ecilasun/tinysys/software/emulator/sdcard/jpeg/flowers.jpg

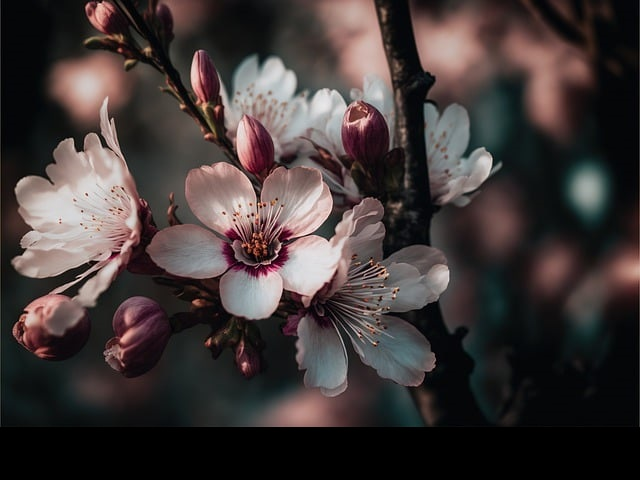
software/emulator/sdcard/jpeg/flowers.jpg
