ecilasun/tinysys/mechanical/expansionboardA.SLDASM

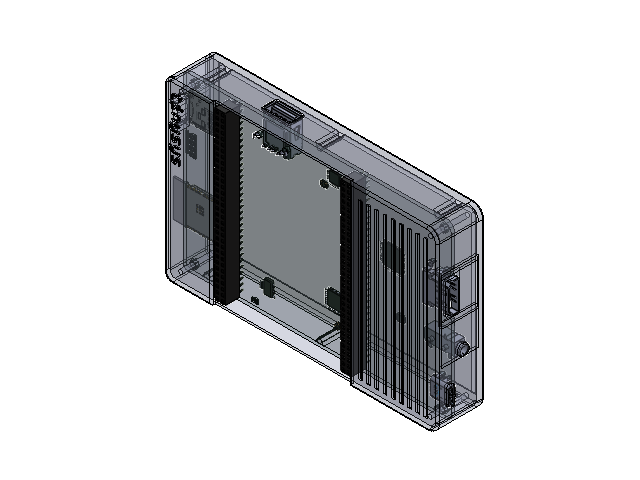
[picture p31: CAD file, 2024-03-18]
mechanical/expansionboardA.SLDASM
CUI_DEVICES_HD02-19-M-MSMT-TR-0
USB4085-GF-A
SJ-3523-SMT-TR-3
LM1117-3
TQFP_64_10x10mm_P05mm
PinSocket_2x32_P254mm_Vertical x 2
LED_1206_3216Metric-5 x 5
DM3AT-SF-PEJM5-6
403WF32015HKR x 2
C32+1
ESP32-C6-WROOM-1_V1
expansionboardA_PCB
Part21^expansionboardA
Part22^expansionboardA
case
