ecilasun/tinysys/software/emulator/sdcard/jpeg/test.jpg

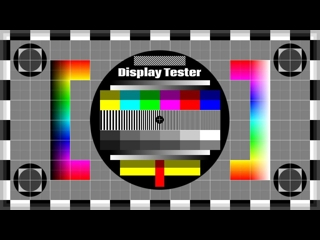
software/emulator/sdcard/jpeg/test.jpg
