ecilasun/tinysys/documents/XILINX-XC7A35T_100T_200T-CORE-BOARD-20220721-V01.pdf

## 5V ONLY

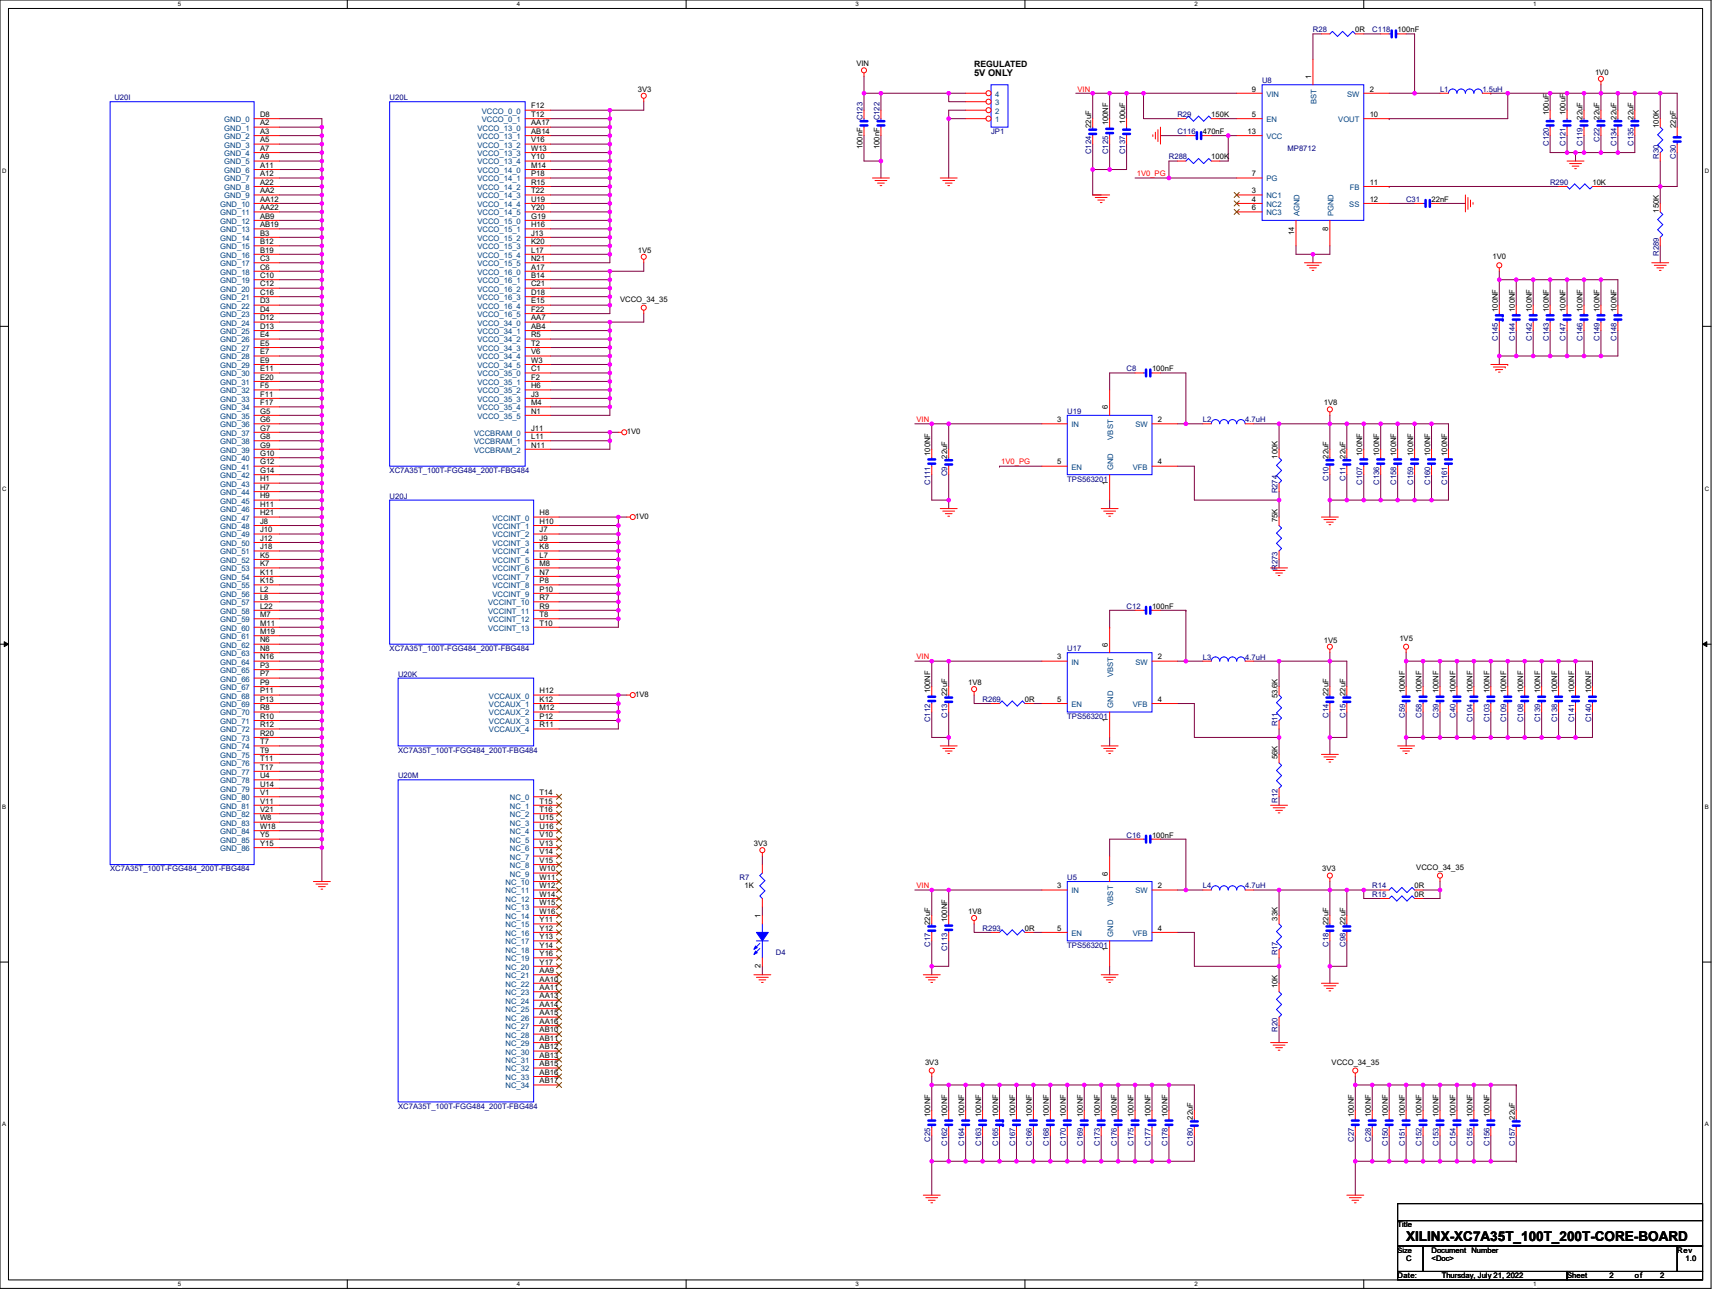
[picture p33: page 1]

Size C C C | Document Number <Doc> | Rev 1.0

Date: Thursday, July 21, 2022 | Sheet 2 of 2

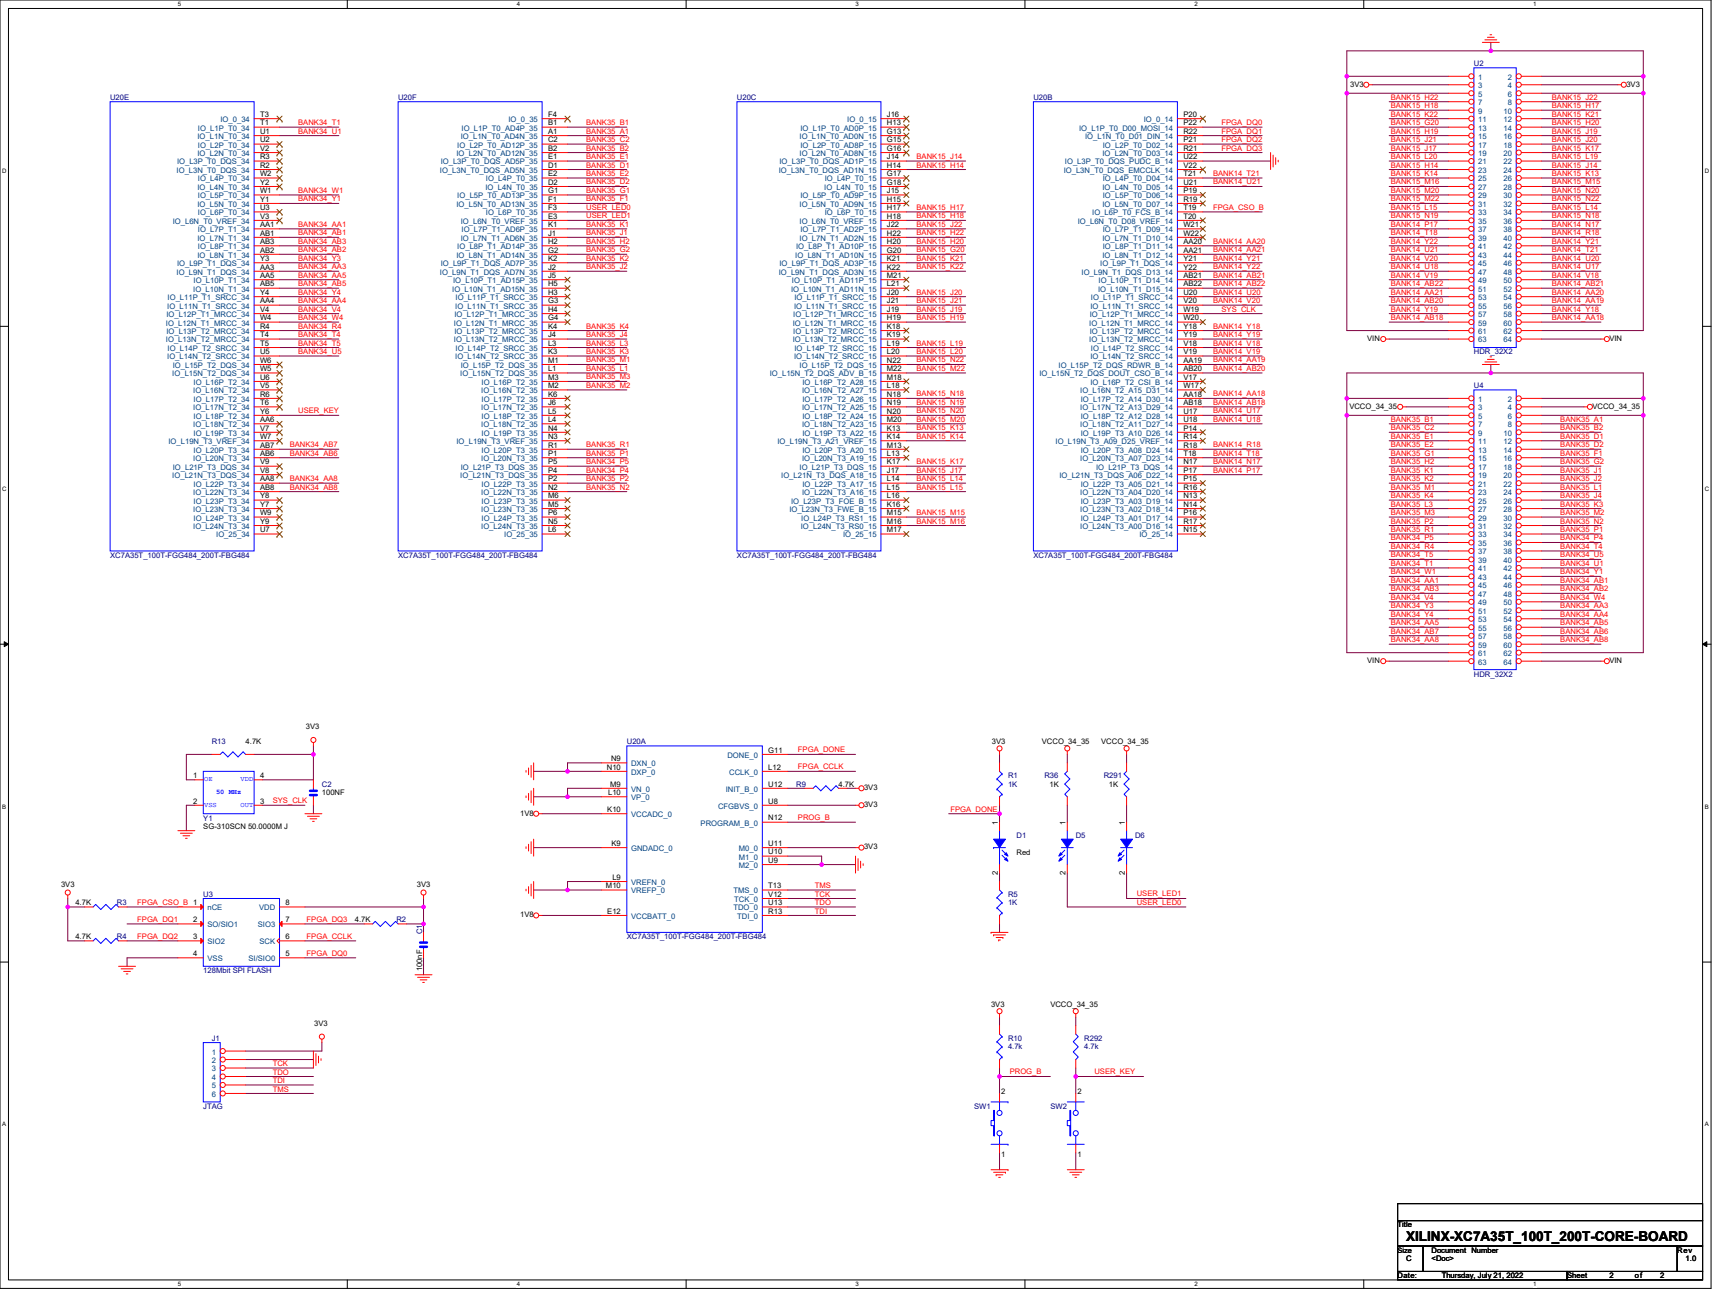
[picture p34: page 2]

D | D

# 100 ohms differential trace

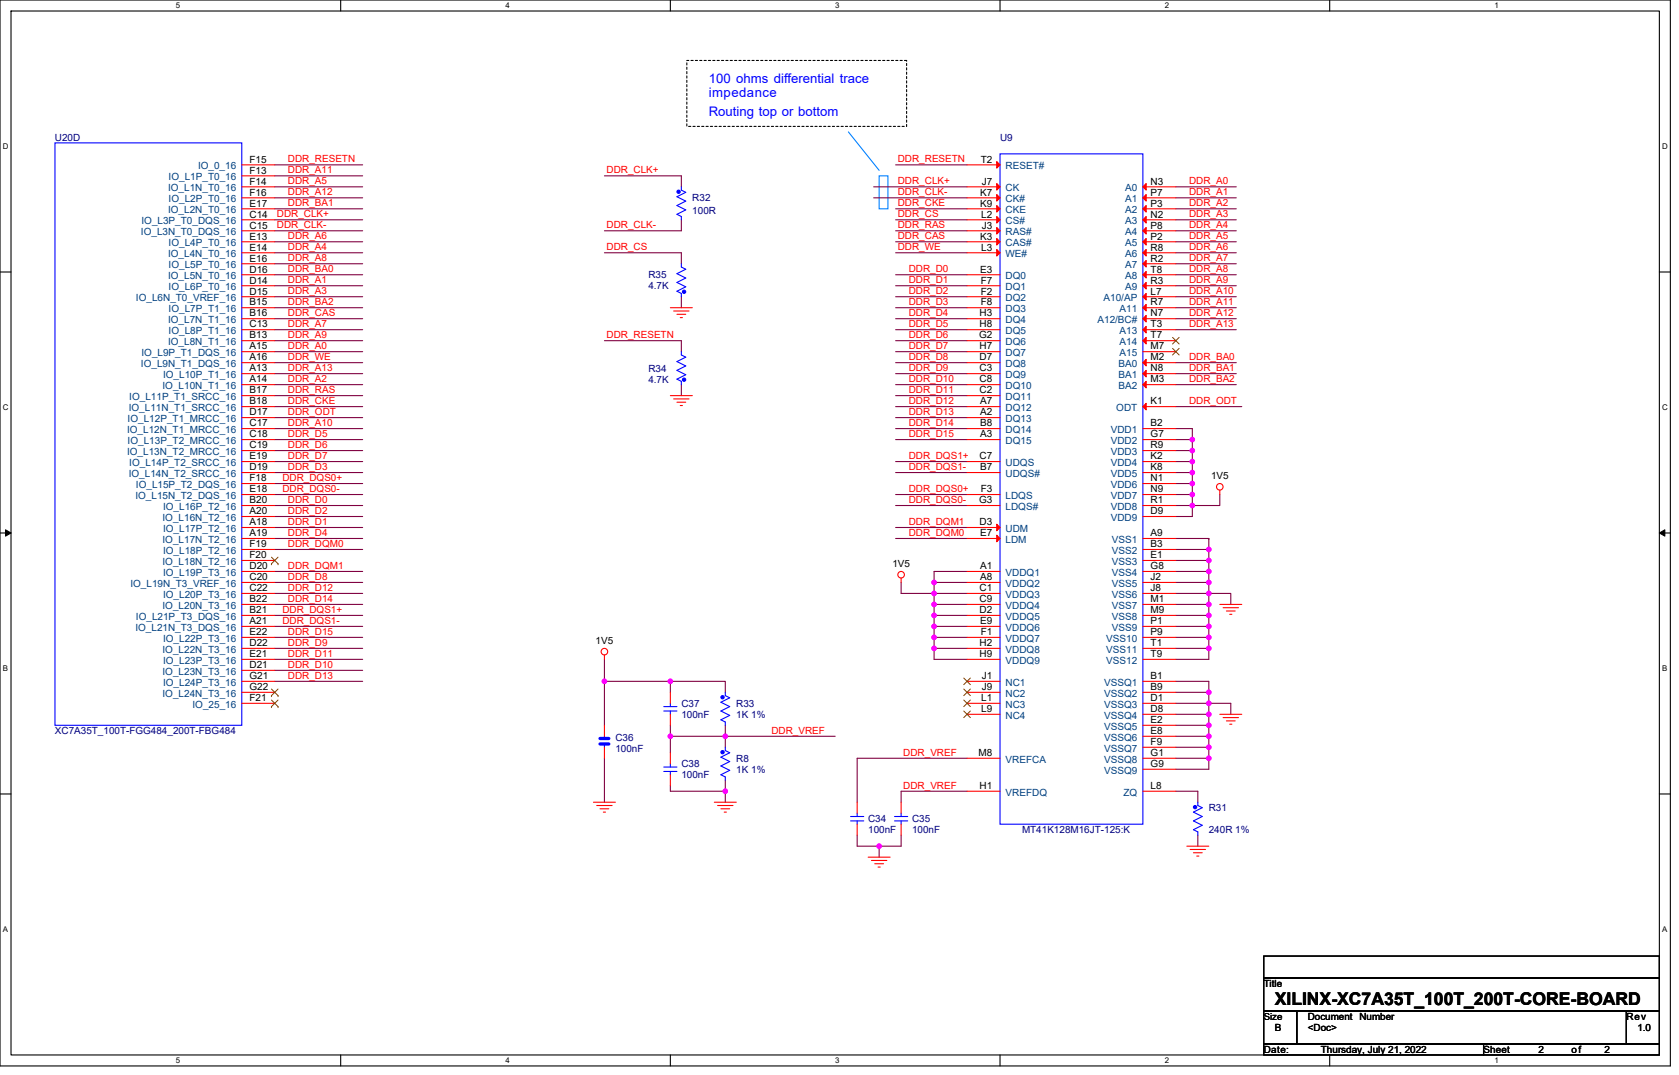
[picture p35: page 3]

impedance
Routing top or bottom

D | D

U20G

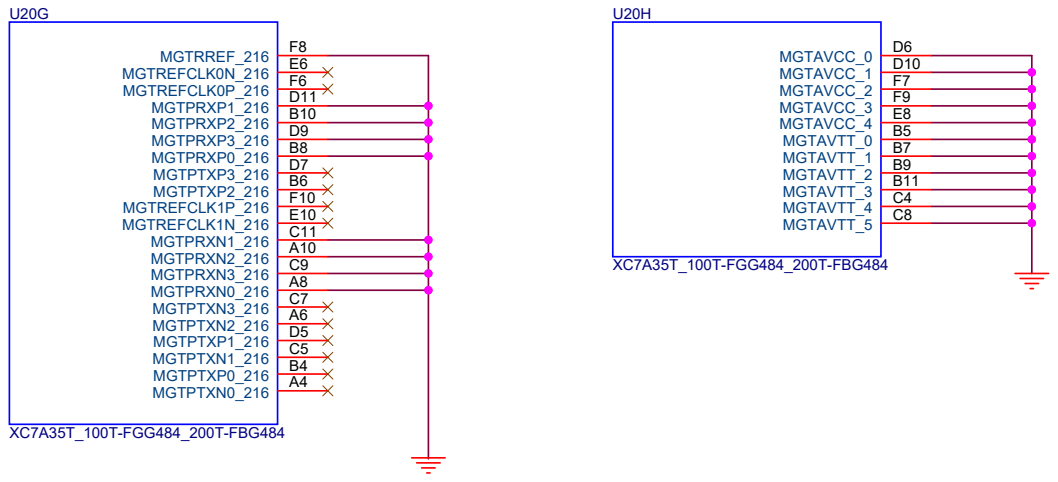
[picture p36: page 4]
