ecilasun/tinysys/software/riscvtool.cpp

#if defined(CAT_LINUX) || defined(CAT_MACOS)
#include <termios.h>
#include <unistd.h>
#else
#include <windows.h>
#endif

#include <stdio.h>
#include <stdlib.h>
#include <string.h>

#include <fcntl.h>
#include <errno.h>

#include <chrono>
#include <thread>
#include <filesystem>

#include "lz4.h"

#if defined(CAT_LINUX) || defined(CAT_MACOS)
#include <sys/ioctl.h>
//char devicename[512] = "/dev/ttyUSB0";
char devicename[512] = "/dev/ttyACM0";
#else // CAT_WINDOWS
#include <conio.h>
// Default COM port is \\.\COM4
char devicename[512] = "\\\\.\\COM4";
#endif

unsigned int getfilelength(const fpos_t &endpos)
{
#if defined(CAT_LINUX)
	return (unsigned int)endpos.__pos;
#elif defined(CAT_MACOS)
	return (unsigned int)endpos;
#else // CAT_WINDOWS
	return (unsigned int)endpos;
#endif
}

class CSerialPort{
	public:

	CSerialPort() { }
	~CSerialPort() { }

	bool Open()
	{
#if defined(CAT_LINUX) || defined(CAT_MACOS)
		// Open COM port
		serial_port = open(devicename, O_RDWR);
		if (serial_port < 0 )
		{
			printf("Error %i from open('%s'): %s\nPlease try another COM port path.\n", errno, devicename, strerror(errno));
			return false;
		}

		struct termios tty;
		if(tcgetattr(serial_port, &tty) != 0)
		{
			printf("Error %i from tcgetattr: %s\nPlease make sure your user has access to the COM device %s.\n", errno, strerror(errno), devicename);
			return false;
		}

		// Set tty. flags
		tty.c_cflag &= ~PARENB; // No parity
		tty.c_cflag &= ~CSTOPB; // One stop bit
		tty.c_cflag &= ~CSIZE;
		tty.c_cflag |= CS8; // 8 bits
		tty.c_cflag &= ~CRTSCTS;
		tty.c_cflag |= CREAD | CLOCAL; // Not model (local), write

		tty.c_lflag &= ~ICANON;
		tty.c_lflag &= ~ECHO;
		tty.c_lflag &= ~ISIG;
		tty.c_iflag &= ~(IXON | IXOFF | IXANY);
		tty.c_iflag &= ~(IGNBRK|BRKINT|PARMRK|ISTRIP|INLCR|IGNCR|ICRNL);

		tty.c_oflag &= ~OPOST;
		tty.c_oflag &= ~ONLCR;
		//tty.c_oflag &= ~OXTABS;
		//tty.c_oflag &= ~ONOEOT;

		tty.c_cc[VTIME] = 50;
		tty.c_cc[VMIN] = 10;

		cfsetispeed(&tty, 460800);
		cfsetospeed(&tty, 460800); // or only cfsetspeed(&tty, B460800);

		if (tcsetattr(serial_port, TCSANOW, &tty) != 0)
			printf("Error %i from tcsetattr: %s\n", errno, strerror(errno));

		printf("%s open\n", devicename);
		return true;

#else // CAT_WINDOWS
		hComm = CreateFileA(devicename, GENERIC_READ | GENERIC_WRITE, 0, 0, OPEN_EXISTING, FILE_ATTRIBUTE_NORMAL, nullptr);
		if (hComm != INVALID_HANDLE_VALUE)
		{
			serialParams.DCBlength = sizeof(serialParams);
			if (GetCommState(hComm, &serialParams))
			{
				serialParams.BaudRate = /*CBR_*/460800;		// 460800 baud
				serialParams.fBinary = true;
				serialParams.fDtrControl = DTR_CONTROL_DISABLE;
				serialParams.fRtsControl = RTS_CONTROL_DISABLE;
				serialParams.fParity = 0;
				serialParams.ByteSize = 8;				// 8 bit bytes
				serialParams.StopBits = ONESTOPBIT;		// 1 stop bit
				serialParams.Parity = NOPARITY;			// no parity
				serialParams.fOutX = 0;					// no xon/xoff
				serialParams.fInX = 0;
				if (SetCommState(hComm, &serialParams) != 0)
				{
					printf("%s open\n", devicename);
					timeouts.ReadIntervalTimeout = MAXDWORD;
					timeouts.ReadTotalTimeoutConstant = 0;
					timeouts.ReadTotalTimeoutMultiplier = 0;
					timeouts.WriteTotalTimeoutConstant = 0;
					timeouts.WriteTotalTimeoutMultiplier = 0;
					if (SetCommTimeouts(hComm, &timeouts) != 0)
						return true;
					else
						printf("ERROR: can't set communication timeouts\n");
				}
				else
					printf("ERROR: can't set communication parameters\n");
			}
			else
				printf("ERROR: can't get communication parameters\n");
		}
		else
			printf("ERROR: can't open COM port %s\n", devicename);
		return false;
#endif
	}

	uint32_t Receive(void *_target, unsigned int _rcvlength)
	{
#if defined(CAT_LINUX) || defined(CAT_MACOS)
		int n = read(serial_port, _target, _rcvlength);
		if (n < 0)
			printf("ERROR: read() failed\n");
		return n;
#else
		DWORD bytesread = 0;
		BOOL success = ReadFile(hComm, _target, _rcvlength, &bytesread, nullptr);
		return success ? bytesread : 0;
#endif
	}

	uint32_t Send(void *_sendbytes, unsigned int _sendlength)
	{
#if defined(CAT_LINUX) || defined(CAT_MACOS)
		int n = write(serial_port, _sendbytes, _sendlength);
		if (n < 0)
			printf("ERROR: write() failed\n");
		return n;
#else // CAT_WINDOWS
		DWORD byteswritten = 0;
		// Send the command
		BOOL success = WriteFile(hComm, _sendbytes, _sendlength, &byteswritten, nullptr);
		if (!success)
			printf("ERROR: write() failed\n");
		return success ? (uint32_t)byteswritten : 0;
#endif
	}

	void Close()
	{
#if defined(CAT_LINUX) || defined(CAT_MACOS)
		close(serial_port);
#else // CAT_WINDOWS
		CloseHandle(hComm);
#endif
	}

#if defined(CAT_LINUX) || defined(CAT_MACOS)
	int serial_port{-1};
#else // CAT_WINDOWS
	HANDLE hComm{INVALID_HANDLE_VALUE};
	DCB serialParams{0};
	COMMTIMEOUTS timeouts{0};
#endif
};

#pragma pack(push,1)
struct SElfFileHeader32
{
	unsigned int m_Magic;       // Magic word (0x7F followed by 'ELF' -> 0x464C457F)
	unsigned char m_Class;
	unsigned char m_Data;
	unsigned char m_EI_Version;
	unsigned char m_OSABI;
	unsigned char m_ABIVersion;
	unsigned char m_Pad[7];
	unsigned short m_Type;      // NONE(0x00)/REL(0x01)/EXEC(0x02)/DYN(0x03)/CORE(0x04)/LOOS(0xFE00)/HIOS(0xFEFF)/LOPROC(0xFF00)/HIPROC(0xFFFF)
	unsigned short m_Machine;   // RISC-V: 0xF3
	unsigned int m_Version;
	unsigned int m_Entry;
	unsigned int m_PHOff;       // Program header offset in file
	unsigned int m_SHOff;
	unsigned int m_Flags;
	unsigned short m_EHSize;
	unsigned short m_PHEntSize;
	unsigned short m_PHNum;
	unsigned short m_SHEntSize;
	unsigned short m_SHNum;
	unsigned short m_SHStrndx;
};
struct SElfProgramHeader32
{
	unsigned int m_Type;
	unsigned int m_Offset;      // Offset of entry point
	unsigned int m_VAddr;
	unsigned int m_PAddr;
	unsigned int m_FileSz;
	unsigned int m_MemSz;       // Length of code in memory (includes code and data sections)
	unsigned int m_Flags;
	unsigned int m_Align;
};
struct SElfSectionHeader32
{
	unsigned int m_NameOffset;
	unsigned int m_Type;
	unsigned int m_Flags;
	unsigned int m_Addr;
	unsigned int m_Offset;
	unsigned int m_Size;
	unsigned int m_Link;
	unsigned int m_Info;
	unsigned int m_AddrAlign;
	unsigned int m_EntSize;
};
#pragma pack(pop)

#define EAlignUp(_x_, _align_) ((_x_ + (_align_ - 1)) & (~(_align_ - 1)))

void parseelfheader(FILE *_op, unsigned char *_elfbinary, unsigned int _filebytesize, unsigned int groupsize, bool includeCOEHeader, bool dumpBinary)
{
	SElfFileHeader32 *fheader = (SElfFileHeader32 *)_elfbinary;

	if (fheader->m_Magic != 0x464C457F)
	{
		printf("Unknown magic, expecting 0x7F followed by 'ELF', got '%c%c%c%c' (%.8X)\n", fheader->m_Magic&0x000000FF, (fheader->m_Magic&0x0000FF00)>>8, (fheader->m_Magic&0x00FF0000)>>16, (fheader->m_Magic&0xFF000000)>>24, fheader->m_Magic);
		return;
	}

	// Gather a block large enough to fit everything
	uint32_t workblocksize = 0;
	for (uint32_t ph=0; ph<fheader->m_PHNum; ++ph)
	{
		SElfProgramHeader32 *pheader = (SElfProgramHeader32 *)(_elfbinary+fheader->m_PHOff+fheader->m_PHEntSize*ph);
		workblocksize += pheader->m_MemSz;
	}
	if (workblocksize == 0)
	{
		printf("Error: estimated output binary size is zero\n");
		return;
	}

	uint32_t *workblock = new uint32_t[workblocksize/4 + 16];

	if (includeCOEHeader)
		fprintf(_op, "memory_initialization_radix=16;\nmemory_initialization_vector=\n");

	int totalout = 0;
	for (uint32_t ph=0; ph<fheader->m_PHNum; ++ph)
	{
		SElfProgramHeader32 *pheader = (SElfProgramHeader32 *)(_elfbinary+fheader->m_PHOff+fheader->m_PHEntSize*ph);

		totalout += pheader->m_MemSz/4;
		if (pheader->m_MemSz != 0)
		{
			int woffset = (pheader->m_PAddr-fheader->m_Entry)/4;

			unsigned int *litteendian = (unsigned int *)(_elfbinary+pheader->m_Offset);

			// Reset blank space
			memset(workblock, 0x0, sizeof(uint32_t)*pheader->m_MemSz/4);

			// Fill rest with data from file
			if (groupsize == 4) // 32bit groups (4 bytes)
			{
				for (unsigned int i=0; i<pheader->m_FileSz/4; ++i)
				{
					workblock[(woffset&0xFFFFFFFC) + (woffset%4)] = litteendian[i];
					woffset++;
				}
			}
			else if (groupsize == 16) // 128bit groups (16 bytes)
			{
				for (unsigned int i=0; i<pheader->m_FileSz/4; ++i)
				{
					workblock[(woffset&0xFFFFFFFC) + (3-(woffset%4))] = litteendian[i];
					woffset++;
				}
			}
			else if (groupsize == 32) // 256bit groups (32 bytes)
			{
				for (unsigned int i=0; i<pheader->m_FileSz/4; ++i)
				{
					workblock[(woffset&0xFFFFFFF8) + (7-(woffset%8))] = litteendian[i];
					woffset++;
				}
			}
		}
	}

	// Pad to avoid misaligned data
	if (groupsize == 4)
		totalout = EAlignUp(totalout, groupsize);
	if (groupsize == 16)
		totalout = EAlignUp(totalout, groupsize/4);
	if (groupsize == 32)
		totalout = EAlignUp(totalout, groupsize/8);

	if (dumpBinary)
	{
		for(int i=0; i<totalout; ++i)
		{
			uint32_t dat = workblock[i];
			fwrite(&dat, 4, 1, _op);
		}
	}
	else
	{
		for(int i=0; i<totalout; ++i)
		{
			int breakpoint = (i!=0) && (groupsize == 4 ? 1 : (groupsize == 16 ? (i%4==0) : (groupsize == 32 ? (i%8==0) : 0)));
			if (breakpoint)
				fprintf(_op, "\n");
			fprintf(_op, "%.8X", workblock[i]);
		}
	}

	delete [] workblock;

	if (includeCOEHeader)
		fprintf(_op, ";");
}

void dumpelf(char *_filename, char *_outfilename, unsigned int groupsize, bool includeCOEHeader, bool dumpBinary)
{
	FILE *fp;
	fp = fopen(_filename, "rb");
	if (!fp)
	{
		printf("ERROR: can't open ELF file %s\n", _filename);
		return;
	}

	FILE *op = fopen(_outfilename, "wb");
	if (!op)
	{
		printf("ERROR: can't open output file %s\n", _outfilename);
		return;
	}

	unsigned int filebytesize = 0;
	fpos_t pos, endpos;
	fgetpos(fp, &pos);
	fseek(fp, 0, SEEK_END);
	fgetpos(fp, &endpos);
	fsetpos(fp, &pos);
	filebytesize = getfilelength(endpos);

	// TODO: Actual binary to send starts at 0x1000
	unsigned char *bytestosend = new unsigned char[filebytesize];
	fread(bytestosend, 1, filebytesize, fp);
	fclose(fp);

	parseelfheader(op, bytestosend, filebytesize, groupsize, includeCOEHeader, dumpBinary);

	fclose(op);

	delete [] bytestosend;
}

bool WACK(CSerialPort &serial, const uint8_t waitfor, uint8_t& received)
{
	int ack = 0;
	uint8_t dummy;
	uint8_t bytes = 0;
	uint32_t timeout = 0;
	do
	{
		if (serial.Receive(&dummy, 1))
		{
			received = dummy;
			++bytes;
			if (dummy == waitfor)
				ack = 1; // Valid ACK
		}
		std::this_thread::sleep_for(std::chrono::milliseconds(5));
		++timeout;
	} while (!bytes);

	return (timeout>16384) ? false : (ack ? true : false);
}

uint64_t WCHK(CSerialPort &serial)
{
	int ack = 0;
	uint64_t extChecksum = 2166136261U;
	do
	{
		std::this_thread::sleep_for(std::chrono::milliseconds(5));
		if (serial.Receive(&extChecksum, 8))
			ack = 1;
	} while (!ack);

	return extChecksum;
}

uint64_t AccumulateHash(const uint64_t inhash, const uint8_t byte)
{
	return 16777619U * inhash ^ (uint64_t)byte;
}

void ConsumeInitialTraffic(CSerialPort& serial)
{
	// When we first open the port, ESP32 will respond with a "ESP-ROM:esp32xxxxxx" and tinysys version message
	// or sometimes with nothing. We need to consume this traffic before we can send any commands
	uint8_t startup = 0;
	while (serial.Receive(&startup, 1))
	{
		// This usually reads something similar to "ESP-ROM:esp32s3-*"
		// It is likely that some other unfinished traffic will show up here
		printf("%c", startup);
	}
}

void sendcmd(int startarg, int argc, char **argv)
{
	CSerialPort serial;
	if (serial.Open() == false)
		return;

	ConsumeInitialTraffic(serial);

	uint8_t received;

	// Start the receiver app on the other end
	char tmpstring[64];
	for (int i=startarg; i<argc; ++i)
	{
		snprintf(tmpstring, 64, "%s", argv[i]);
		serial.Send((uint8_t*)tmpstring, strlen(argv[i]));
		std::this_thread::sleep_for(std::chrono::milliseconds(50));
		if (i!=argc-1)
			serial.Send((void*)" ", 1); // Add spaces in between arguments
	}
	snprintf(tmpstring, 64, "\n");
	serial.Send((uint8_t*)tmpstring, 1); // Include return character and space

	serial.Close();
}

// This is meant to be used with the receiver app on the tinysys side
// It will send the file in chunks after header information
// The receiver app will respond with an ack(+) or error(!) to each request
void sendfile(char *_filename)
{
	char tmpstring[129];

	FILE *fp;
	fp = fopen(_filename, "rb");
	if (!fp)
	{
		printf("ERROR: can't open ELF file %s\n", _filename);
		return;
	}

	char cleanfilename[129];
	{
		using namespace std::filesystem;
		path p = absolute(_filename);
		strcpy(cleanfilename, p.filename().string().c_str());
	}

	unsigned int filebytesize = 0;
	fpos_t pos, endpos;
	fgetpos(fp, &pos);
	fseek(fp, 0, SEEK_END);
	fgetpos(fp, &endpos);
	fsetpos(fp, &pos);
	filebytesize = getfilelength(endpos);

	uint8_t *filedata = new uint8_t[filebytesize + 64];
	fread(filedata, 1, filebytesize, fp);
	fclose(fp);

	CSerialPort serial;
	if (serial.Open() == false)
	{
		delete [] filedata;
		return;
	}

	// Send the file bytes in chunks
	uint32_t packetSize = 1024;
	int worstSize = LZ4_compressBound(filebytesize);

	// Pack the data before sending it across
	char* encoded = new char[worstSize];
	uint32_t encodedSize = LZ4_compress_default((const char*)filedata, encoded, filebytesize, worstSize);
	printf("Compression ratio = %.2f%% (%d->%d bytes)\n", 100.f*float(encodedSize)/float(filebytesize), filebytesize, encodedSize);

	// Now we can work out how many packets we need to send
	uint32_t numPackets = encodedSize / packetSize;
	uint32_t leftoverBytes = encodedSize % packetSize;

	uint8_t received;

	ConsumeInitialTraffic(serial);

	// Start the receiver app on the other end
	snprintf(tmpstring, 128, "recv");
	serial.Send((uint8_t*)tmpstring, 4);
	std::this_thread::sleep_for(std::chrono::milliseconds(50));
	snprintf(tmpstring, 128, "\n");
	serial.Send((uint8_t*)tmpstring, 1);
	if (!WACK(serial, '+', received))
	{
		printf("Transfer initiation error: '%c'\n", received);
		serial.Close();
		delete [] filedata;
		return;
	}

	// Send encoded length
	uint32_t encodedLen = encodedSize;
	serial.Send(&encodedLen, 4);
	if (!WACK(serial, '+', received))
	{
		printf("Encoded buffer length error: '%c'\n", received);
		serial.Close();
		delete [] filedata;
		return;
	}

	// Send actual length
	uint32_t decodedLen = filebytesize;
	serial.Send(&decodedLen, 4);
	if (!WACK(serial, '+', received))
	{
		printf("Decoded buffer length error: '%c'\n", received);
		serial.Close();
		delete [] filedata;
		return;
	}

	// Send name length
	uint32_t nameLen = strlen(cleanfilename);
	serial.Send(&nameLen, 4);
	if (!WACK(serial, '+', received))
	{
		printf("File name length error: '%c'\n", received);
		serial.Close();
		delete [] filedata;
		return;
	}

	// Send name
	serial.Send(cleanfilename, nameLen);
	if (!WACK(serial, '+', received))
	{
		printf("File name error: '%c'\n", received);
		serial.Close();
		delete [] filedata;
		return;
	}

	uint32_t i = 0;
	uint32_t packetOffset = 0;
	char progress[65];
	for (i=0; i<64; ++i)
		progress[i] = ' ';//176;
	progress[64] = 0;
	printf("Uploading '%s' (packet size: %dx%d+%d bytes, packer buffer: %d bytes)\n", cleanfilename, numPackets, packetSize, leftoverBytes, worstSize);
	for (i=0; i<numPackets; ++i)
	{
		const char* source = (const char*)(encoded + packetOffset);

		int idx = (i*64)/numPackets;
		for (int j=0; j<=idx; ++j) // Progress bar
			progress[j] = '=';//219;
		printf("\r [%s] %.2f%%\r", progress, (i*100)/float(numPackets));

		if (!WACK(serial, '+', received)) // Wait for a 'go' signal
		{
			printf("Packet size error at %d/%d (%d): '%c'\n", i, numPackets, received, packetSize);
			serial.Close();
			delete [] filedata;
			return;
		}

		serial.Send(&packetSize, 4);

		if (!WACK(serial, '+', received)) // Wait for a 'go' signal
		{
			printf("Packet error at %d/%d (%d): '%c'\n", i, numPackets, received, packetSize);
			serial.Close();
			delete [] filedata;
			return;
		}

		serial.Send((void*)source, packetSize);

		packetOffset += packetSize;
	}

	if (leftoverBytes)
	{
		const char* source = (const char*)(encoded + packetOffset);

		for (int j=0; j<64; ++j) // Progress bar
			progress[j] = '=';//219;
		printf("\r [%s] %.2f%%\r", progress, 100.0f);

		if (!WACK(serial, '+', received)) // Wait for a 'go' signal
		{
			printf("Packet size error at %d/%d (%d): '%c'\n", i, numPackets, received, packetSize);
			serial.Close();
			delete [] filedata;
			return;
		}

		serial.Send(&leftoverBytes, 4);

		if (!WACK(serial, '+', received)) // Wait for a 'go' signal
		{
			printf("Packet error at %d/%d (%d): '%c'\n", i, numPackets, received, packetSize);
			serial.Close();
			delete [] filedata;
			return;
		}

		serial.Send((void*)source, leftoverBytes);

		packetOffset += leftoverBytes;
	}

	printf("\r\n");

	delete[] encoded;

	serial.Close();
	printf("%d bytes uploaded\n", packetOffset);

	delete [] filedata;
}

void resetCPUs()
{
	CSerialPort serial;
	if (serial.Open() == false)
	{
		serial.Close();
		return;
	}

	ConsumeInitialTraffic(serial);

	// Send reset request
	char tmpstring[4];
	tmpstring[0] = '~';
	serial.Send((uint8_t*)tmpstring, 1);

	serial.Close();
	printf("CPUs reset\n");
}

void terminal()
{
	CSerialPort serial;
	if (serial.Open() == false)
	{
		serial.Close();
		return;
	}

	ConsumeInitialTraffic(serial);

	// Terminal loop
	uint8_t received[4096];

	//fcntl(0, F_SETFL, fcntl(0, F_GETFL) | O_NONBLOCK);
#ifdef CAT_LINUX
    termios term;
    tcgetattr(0, &term);
    termios term2 = term;
    term2.c_lflag &= ~(ICANON | ECHO);
    tcsetattr(0, TCSANOW, &term2);
#endif

	uint8_t ctrlcchar = 3;
	do {
		uint32_t bytesReceived = serial.Receive(&received, 4096);
		for (uint32_t i=0; i<bytesReceived; ++i)
			printf("%c", received[i]);
#if defined(CAT_LINUX) || defined(CAT_MACOS)
    	int byteswaiting;
    	ioctl(0, FIONREAD, &byteswaiting);
		if (byteswaiting)
		{
			unsigned char chr;
			int nread = read(0,&chr,1);
			//serial.Send((uint8_t*)&chr, 1);
			// Echo back
			printf("%c", chr);
			fflush(stdout);
			if (chr == 13)
				printf("%c", 10);
		}
#else
		if (_kbhit())
		{
			int chr = _getch();
			if (chr == 27) // ESC
				serial.Send(&ctrlcchar, 1);
			else
				serial.Send((uint8_t*)&chr, 1);
			// Echo back
			printf("%c", chr);
			if (chr == 13)
				printf("%c", 10);
		}
#endif
	} while (true);

#ifdef CAT_LINUX
	tcsetattr(0, TCSANOW, &term);
#endif

	serial.Close();
}

void showusage()
{
	printf("Usage:\n");
	printf("riscvtool -terminal [usbdevicename]\n  Go into terminal mode to interact with the target device\n");
	printf("riscvtool -reset [usbdevicename]\n  Send a reset command to the target device\n");
	printf("riscvtool -sendcmd [usbdevicename] command\n  Send a command to the target device\n");
	printf("riscvtool -sendfile [usbdevicename] binaryfilename\n  Send a binary file to the target device\n");
	printf("riscvtool -makerom binaryfilename groupbytesize outputfilename\n  Generate a ROM file from an ELF binary. This is a COE format file, which is no longer used by newer versions of tinysys and is kept as legacy\n");
	printf("riscvtool -makemem binaryfilename groupbytesize outputfilename\n  Generate a memory initialization file for FPGA from an ELF binary. This is used when building a new hardware device with an embedded ROM image\n");
	printf("riscvtool -makebin binaryfilename groupbytesize outputfilename\n  Generate a loadable binary image from an ELF binary. It is often used to test ROM images by dropping this into the boot folder on the device\n");
	printf("NOTE: Default device name is %s\n", devicename);
}

int main(int argc, char **argv)
{
	if (argc==1)
	{
		printf("RISCVTool 1.1H\n");
		showusage();
		return 0;
	}

	int i=1;
	if (argc>=2 && strstr(argv[i++], "-reset"))
	{
		if (argc > 2)
			strcpy(devicename, argv[i++]);
		resetCPUs();
		return 0;
	}

	i=1;
	if (argc>=3 && strstr(argv[i++], "-sendcmd"))
	{
		if (argc > 3)
			strcpy(devicename, argv[i++]);
		sendcmd(i, argc, argv);
		return 0;
	}

	i=1;
	if (argc>=3 && strstr(argv[i++], "-sendfile"))
	{
		if (argc > 3)
			{strcpy(devicename, argv[i++]); printf("Device: %s\n", devicename);}
		printf("Sending file %s\n", argv[i]);
		sendfile(argv[i++]);
		return 0;
	}

	i=1;
	if (argc>=2 && strstr(argv[i++], "-terminal"))
	{
		if (argc > 2)
			strcpy(devicename, argv[i++]);
		terminal();
		return 0;
	}

	i=1;
	if (argc>=3 && strstr(argv[i++], "-makerom"))
	{
		unsigned int groupsize = (unsigned int)strtoul(argv[3], nullptr, 10);
		dumpelf(argv[2], argv[4], groupsize, true, false);
		return 0;
	}

	i=1;
	if (argc>=3 && strstr(argv[i++], "-makemem"))
	{
		unsigned int groupsize = (unsigned int)strtoul(argv[3], nullptr, 10);
		dumpelf(argv[2], argv[4], groupsize, false, false);
		return 0;
	}

	i=1;
	if (argc>=3 && strstr(argv[i++], "-makebin"))
	{
		unsigned int groupsize = (unsigned int)strtoul(argv[3], nullptr, 10);
		dumpelf(argv[2], argv[4], groupsize, false, true);
		return 0;
	}

	printf("RISCVTool 1.1H\n");
	printf("Error: Unknown arguments.\n");
	showusage();

	return 0;
}
