ecilasun/tinysys/software/ostools/recv/recv.cpp

/** \file
 * File reception utility for TinyOS
 * \ingroup TinyOS
 * This command should be placed in sys/bin and will be initiated remotely to kick off a file transfer.
 */

#include "basesystem.h"
#include "core.h"
#include "uart.h"
#include "vpu.h"
#include "task.h"
#include "encoding.h"
#include "mini-printf.h"
#include "serialinringbuffer.h"
#include "lz4.h"

#include <stdio.h>
#include <string.h>
#include <stdlib.h>

int main()
{
	// Disable OS UART interrupt handling
	UARTInterceptSetState(1);

	// NOTE: We have to be absolutely still with the UART chatter as the other side will not tolerate any noise other than ACK/NACK
	const char* NACK = "!";
	const char* ACK = "+";

	// Emulator can still receive files over net/UART proxy
	/*uint32_t isEmulator = read_csr(0xF12) & 0x80000000 ? 0 : 1; // CSR_MARCHID is 0x80000000 for read hardware, 0x00000000 for emulator
	if (isEmulator)
	{
		UARTPrintf("! Emulator detected, cannot receive files\n");
		return 0;
	}*/

	// Wait for UART chatter to finish
	E32Sleep(HUNDRED_MILLISECONDS_IN_TICKS);

	// At startup, acknowledge the sender so that it can start sending the file header
	UARTSendBlock((uint8_t*)ACK, 1);

	// Grab the encoded size
	uint32_t encodedLen = 0;
	for (uint32_t i=0;i<4;)
	{
		uint8_t byte;
		if (SerialInRingBufferRead(&byte, 1))
		{
			encodedLen |= (byte << (i*8));
			++i;
		}
	}
	UARTSendBlock((uint8_t*)ACK, 1);

	// Grab the file size size
	uint32_t decodedLen = 0;
	for (uint32_t i=0;i<4;)
	{
		uint8_t byte;
		if (SerialInRingBufferRead(&byte, 1))
		{
			decodedLen |= (byte << (i*8));
			++i;
		}
	}
	UARTSendBlock((uint8_t*)ACK, 1);

	// Grab the file name length
	uint32_t fileNameLen = 0;
	for (uint32_t i=0;i<4;)
	{
		uint8_t byte;
		if (SerialInRingBufferRead(&byte, 1))
		{
			fileNameLen |= (byte << (i*8));
			++i;
		}
	}

	if (fileNameLen > 63)
	{
		// Respond to the sender with an error code as the file name is too long
		UARTSendBlock((uint8_t*)NACK, 1);
		return 0;
	}
	else
		UARTSendBlock((uint8_t*)ACK, 1);

	// Grab the file name
	char fileName[96];
	for (uint32_t i=0;i<fileNameLen;)
	{
		if (SerialInRingBufferRead(&fileName[i], 1))
			++i;
	}
	// Null-terminate the file name
	fileName[fileNameLen] = 0;

	// Send ready to receive file
	UARTSendBlock((uint8_t*)ACK, 1);

	uint8_t* sourceBuffer = new uint8_t[encodedLen+64];

	uint32_t bytesReceived = 0;
	do
	{
		// Let the sender know we're ready for the packet size
		UARTSendBlock((uint8_t*)ACK, 1);

		// Receive packet size
		uint32_t packetLen = 0;
		for (uint32_t i=0;i<4;)
		{
			uint8_t byte;
			if (SerialInRingBufferRead(&byte, 1))
			{
				packetLen |= (byte << (i*8));
				++i;
			}
		}

		if (packetLen == 0)
		{
			printf("File transfer aborted, file wasn't saved\n");
			return 0;
		}

		// Let the sender know we're ready for the packet data
		UARTSendBlock((uint8_t*)ACK, 1);

		// Receive encoded bytes
		for (uint32_t j=0; j<packetLen;)
		{
			uint8_t byte;
			if (SerialInRingBufferRead(&byte, 1))
			{
				sourceBuffer[bytesReceived+j] = byte;
				++j;
			}
		}

		bytesReceived += packetLen;
	}
	while(bytesReceived < encodedLen);

	uint8_t* targetBuffer = new uint8_t[decodedLen+512];
	int unpacked = LZ4_decompress_safe((const char*)sourceBuffer, (char*)targetBuffer, bytesReceived, decodedLen+512);
	if (unpacked > 0)
	{
		// Dump the new data to a temp file
		FILE *fp = fopen("downloaded.bin", "wb");
		if (fp)
		{
			printf("Saving file...");

			/*uint32_t written = (uint32_t)*/fwrite(targetBuffer, 1, decodedLen, fp);
			fclose(fp);

			// Remove the file if it already exits
			remove(fileName);

			// Rename the temp file to the original file name
			rename("downloaded.bin", fileName);
			printf("done\n");
		}
		else
			printf("! ERROR: can't create file %s\n", fileName);
	}
	else
	{
		printf("! ERROR: decompression failed (received:%d, unpacked:%d, originalpacked:%d, originalunpacked:%d)\n", (int)bytesReceived, (int)unpacked, (int)encodedLen, (int)decodedLen);
	}

	delete [] sourceBuffer;
	delete [] targetBuffer;

    return 0;
}
