ecilasun/tinysys/hardware/tinysys.srcs/sources_1/new/vpu.sv

`timescale 1ns / 1ps
`default_nettype none

import axi4pkg::*;

module videocore(
	input wire aclk,
	input wire clk25,
	input wire clk125,
	input wire aresetn,
	input wire rst25n,
	axi4if.master m_axi,
	output wire HDMI_CLK_p,
	output wire HDMI_CLK_n,
	output wire [2:0] HDMI_TMDS_p,
	output wire [2:0] HDMI_TMDS_n,
	//input wire HDMI_CEC,
	//inout wire HDMI_SDA,
	//inout wire HDMI_SCL,
	//input wire HDMI_HPD,
	input wire audioclock,
	input wire [31:0] audiosampleLR,
	input wire vpufifoempty,
	input wire [31:0] vpufifodout,
	output wire vpufifore,
	input wire vpufifovalid,
	output wire [31:0] vpustate);

// --------------------------------------------------
// Reset delay line
// --------------------------------------------------

wire delayedresetn;
delayreset delayresetinst(
	.aclk(aclk),
	.inputresetn(aresetn),
	.delayedresetn(delayedresetn) );

wire delayedreset25n;
delayreset delayreset25inst(
	.aclk(clk25),
	.inputresetn(rst25n),
	.delayedresetn(delayedreset25n) );

// --------------------------------------------------
// HDMI video output 640x480 @ 60Hz
// --------------------------------------------------

wire [9:0] video_x;
wire [9:0] video_y;
wire notblank = (video_x < 10'd640) && (video_y < 10'd480);

wire [23:0] rgbdat;
wire [2:0] tmds;
wire tmds_clock;

// "TinySys" "FPGA" "Game" 60Hz 640x480 44.1KHz 16bit
hdmi #(.VIDEO_ID_CODE(1), .IT_CONTENT(1'b1), .VIDEO_REFRESH_RATE(60.0), .VENDOR_NAME({"TinySys", 8'd0}), .PRODUCT_DESCRIPTION({"FPGA", 96'd0}), .SOURCE_DEVICE_INFORMATION(8), .AUDIO_RATE(44100), .AUDIO_BIT_WIDTH(16)) HDMIInst(
    .clk_pixel_x5(clk125),
    .clk_pixel(clk25),
    .clk_audio(audioclock),
    .reset(~delayedreset25n),
    .rgb(rgbdat),
    .audio_sample_word( {audiosampleLR[31:16], audiosampleLR[15:0]} ),
	// HDMI data out
    .tmds(tmds),
    .tmds_clock(tmds_clock),
	// Current pixel position
	.cx(video_x),
    .cy(video_y));

genvar i;
generate
    for (i = 0; i < 3; i++)
    begin: obufds_gen
        OBUFDS #(.IOSTANDARD("TMDS_33")) obufds (.I(tmds[i]), .O(HDMI_TMDS_p[i]), .OB(HDMI_TMDS_n[i]));
    end
    OBUFDS #(.IOSTANDARD("TMDS_33")) obufds_clock(.I(tmds_clock), .O(HDMI_CLK_p), .OB(HDMI_CLK_n));
endgenerate

// --------------------------------------------------
// Scan setup
// --------------------------------------------------

// NOTE: First, set up the scanout address, then enable video scanout
logic [31:0] scanaddr;
logic [31:0] scanoffset;
logic [10:0] scaninc;
logic scanenable;

// --------------------------------------------------
// Common
// --------------------------------------------------

logic cmdre;
assign vpufifore = cmdre;

// --------------------------------------------------
// Setup
// --------------------------------------------------

logic [9:0] lastscanline;
logic [7:0] burstlen;
logic scanwidth;			// 0:320 pixel wide, 1:640 pixel wide
logic colormode;			// 0:indexed color, 1:16bit color


// --------------------------------------------------
// Scanline cache
// --------------------------------------------------

logic [127:0] scanlinecache [0:127];

initial begin
	for (int i=0;i<128;i=i+1) begin
		scanlinecache[i] = 128'd0;
	end
end

wire [127:0] scanlinedout;
logic [127:0] scanlinedin;
logic scanlinewe;
logic [6:0] scanlinewa;
logic [6:0] scanlinera;

always @(posedge aclk) begin
	/*if (~delayedresetn) begin
		
	end else begin*/
		if (scanlinewe)
			scanlinecache[scanlinewa] <= scanlinedin;
	/*end*/
end
assign scanlinedout = scanlinecache[scanlinera];

// --------------------------------------------------
// Output address selection
// --------------------------------------------------

logic [3:0] pixelscanaddr;

always_comb begin
	unique case ({scanwidth, colormode})
		2'b00: begin pixelscanaddr = video_x[4:1];			scanlinera = {2'b0, video_x[9:5]}; end	// 320*240 8bpp
		2'b01: begin pixelscanaddr = {1'b0,video_x[3:1]};	scanlinera = {1'b0, video_x[9:4]}; end	// 320*240 16bpp
		2'b10: begin pixelscanaddr = video_x[3:0];			scanlinera = {1'b0, video_x[9:4]}; end	// 640*480 8bpp
		2'b11: begin pixelscanaddr = {1'b0,video_x[2:0]};	scanlinera = video_x[9:3]; end			// 640*480 16bpp
	endcase
end

// --------------------------------------------------
// Output color
// --------------------------------------------------

logic [11:0] rgbcolor;
logic [7:0] paletteindex;

// Generate actual RGB color for 16bit mode
always_comb begin
	// Pixel data is 12 bits but stored as 16 bits (the spare 4 bits are unused for now, could be utilized as alpha etc
	unique case (pixelscanaddr[2:0])
		//                   R:G:B                    UNUSED
		3'b000: rgbcolor = { scanlinedout[11:0]     }; // scanlinedout[15:12]
		3'b001: rgbcolor = { scanlinedout[27:16]    }; // scanlinedout[31:28]
		3'b010: rgbcolor = { scanlinedout[43:32]    }; // scanlinedout[47:44]
		3'b011: rgbcolor = { scanlinedout[59:48]    }; // scanlinedout[63:60] 
		3'b100: rgbcolor = { scanlinedout[75:64]    }; // scanlinedout[79:76]
		3'b101: rgbcolor = { scanlinedout[91:80]    }; // scanlinedout[95:92]
		3'b110: rgbcolor = { scanlinedout[107:96]   }; // scanlinedout[111:108]
		3'b111: rgbcolor = { scanlinedout[123:112]  }; // scanlinedout[127:124]
	endcase
end

always_comb begin
	unique case (pixelscanaddr)
		4'b0000: paletteindex = scanlinedout[7:0];
		4'b0001: paletteindex = scanlinedout[15:8];
		4'b0010: paletteindex = scanlinedout[23:16];
		4'b0011: paletteindex = scanlinedout[31:24];
		4'b0100: paletteindex = scanlinedout[39:32];
		4'b0101: paletteindex = scanlinedout[47:40];
		4'b0110: paletteindex = scanlinedout[55:48];
		4'b0111: paletteindex = scanlinedout[63:56];
		4'b1000: paletteindex = scanlinedout[71:64];
		4'b1001: paletteindex = scanlinedout[79:72];
		4'b1010: paletteindex = scanlinedout[87:80];
		4'b1011: paletteindex = scanlinedout[95:88];
		4'b1100: paletteindex = scanlinedout[103:96];
		4'b1101: paletteindex = scanlinedout[111:104];
		4'b1110: paletteindex = scanlinedout[119:112];
		4'b1111: paletteindex = scanlinedout[127:120];
	endcase
end

// --------------------------------------------------
// Palette RAM
// --------------------------------------------------

logic [11:0] palettedin;
logic [7:0] palettewa;
logic palettewe;

logic [11:0] paletteentries[0:255];

initial begin
	$readmemh("colorpalette.mem", paletteentries);
end

// Write port
always @(posedge aclk) begin
	if (palettewe)
		paletteentries[palettewa] <= palettedin;
end

// Read port
logic [11:0] paletteout;
always @(posedge clk25) begin
	if (~rst25n) begin
		paletteout <= 12'd0;
	end else begin
		case ({notblank, scanenable, colormode})
			3'b110: paletteout <= paletteentries[paletteindex];
			3'b111: paletteout <= rgbcolor;
			default: paletteout <= 12'd0;
		endcase
	end
end

// 12 bit RGB output expanded to 24 bit (using top 4 bits per component only)
assign rgbdat = {paletteout[11:8], 4'd0, paletteout[7:4], 4'd0, paletteout[3:0], 4'd0};

// --------------------------------------------------
// AXI4 defaults
// --------------------------------------------------

assign m_axi.arsize = SIZE_16_BYTE; // 128bit read bus
assign m_axi.arburst = BURST_INCR;

assign m_axi.awlen = 0;				// one burst
assign m_axi.awsize = SIZE_16_BYTE; // 128bit write bus
assign m_axi.awburst = BURST_INCR;

// NOTE: This unit does not write to memory yet
// TODO: Will do so when raster or DMA unit is online
assign m_axi.awvalid = 0;
assign m_axi.awaddr = 'd0;
assign m_axi.wvalid = 0;
assign m_axi.wstrb = 16'h0000; // For raster unit or DMA, this will be the byte write mask for a 16 pixel horizontal tile
assign m_axi.wlast = 0;
assign m_axi.wdata = 'd0;
assign m_axi.bready = 0;

// --------------------------------------------------
// Command FIFO
// --------------------------------------------------

typedef enum logic [3:0] {
	WCMD, DISPATCH,
	SETVPAGE,
	SETPAL,
	VMODE,
	VSCANSIZE,
	FINALIZE } vpucmdmodetype;
vpucmdmodetype cmdmode = WCMD;

logic [31:0] vpucmd;

always_ff @(posedge aclk) begin
	if (~delayedresetn) begin
		vpucmd <= 32'd0;
		scanaddr <= 32'd0;
		burstlen <= 'd19;
		lastscanline <= 10'd0;
		palettedin <= 12'd0;
		scanenable <= 1'b0;
		cmdre <= 1'b0;
		scanwidth <= 1'b0;
		colormode <= 1'b0;
		palettewe <= 1'b0;
		cmdmode <= WCMD;
		palettewa <= 8'd0;
		scaninc <= 11'd0;
	end else begin
		cmdre <= 1'b0;
		palettewe <= 1'b0;

		case (cmdmode)
			WCMD: begin
				if (vpufifovalid && ~vpufifoempty) begin
					vpucmd <= vpufifodout;
					// Advance FIFO
					cmdre <= 1'b1;
					// Dispatch cmd
					cmdmode <= DISPATCH;
				end
			end

			DISPATCH: begin
				case (vpucmd[7:0])
					8'h00:		cmdmode <= SETVPAGE;	// Set the scanout start address (followed by 32bit cached memory address, 64 byte cache aligned)
					8'h01:		cmdmode <= SETPAL;		// Set 24 bit color palette entry (followed by 8bit address+24bit color in next word)
					8'h02:		cmdmode <= VMODE;		// Set up video mode or turn off scan logic (default is 320x240*8bit paletted)
					default:	cmdmode <= FINALIZE;	// Invalid command, wait one clock and try next
				endcase
			end

			SETVPAGE: begin
				if (vpufifovalid && ~vpufifoempty) begin
					scanaddr <= vpufifodout;	// Set new video scanout address (64 byte cache aligned, as we read in bursts)
					// Advance FIFO
					cmdre <= 1'b1;
					cmdmode <= FINALIZE;
				end
			end

			SETPAL: begin
				if (vpufifovalid && ~vpufifoempty) begin
					palettewe <= 1'b1;
					palettewa <= vpufifodout[31:24];	// 8 bit palette index
					//??? <= vpufifodout[23:16];		// 8 bit extra data, unused
					//??? <= vpufifodout[15:11];		// 4 bit extra data, alpha perhaps?
					palettedin <= vpufifodout[11:0];	// 12 bit color
					// Advance FIFO
					cmdre <= 1'b1;
					cmdmode <= FINALIZE;
				end
			end

			VMODE: begin
				if (vpufifovalid && ~vpufifoempty) begin
					scanenable <= vpufifodout[0];	// 0:video output disabled, 1:video output enabled
					scanwidth <= vpufifodout[1];	// 0:320-wide, 1:640-wide
					colormode <= vpufifodout[2];	// 0:8bit indexed, 1:16bit rgb
					lastscanline <= vpufifodout[1] ? 10'd524 : 10'd523;
					// ? <= vpufifodout[31:3] unused for now

					// Set up burst count to 20 / 40 / 80 depending on video mode
					unique case (vpufifodout[2:1])
						2'b00: burstlen <= 'd19;	// 320*240 8bpp
						2'b01: burstlen <= 'd39;	// 640*480 8bpp
						2'b10: burstlen <= 'd39;	// 320*240 16bpp
						2'b11: burstlen <= 'd79;	// 640*480 16bpp
					endcase

					// Advance FIFO
					cmdre <= 1'b1;
					cmdmode <= VSCANSIZE;
				end
			end

			VSCANSIZE: begin
				unique case (vpufifodout[2:1])
					2'b00: scaninc <= 11'd320;	// 320*240 8bpp
					2'b01: scaninc <= 11'd640;	// 640*480 8bpp
					2'b10: scaninc <= 11'd640;	// 320*240 16bpp
					2'b11: scaninc <= 11'd1280;	// 640*480 16bpp
				endcase
				cmdmode <= FINALIZE;
			end

			FINALIZE: begin
				cmdmode <= WCMD;
			end
		endcase

	end
end

// --------------------------------------------------
// Scan-out logic
// --------------------------------------------------

wire startofrowp = video_x == 10'd0;
wire endofcolumnp = video_y == 10'd490;
wire vsyncnow = startofrowp && endofcolumnp;

logic blankt;
always_ff @(posedge clk25) begin
	if (~rst25n) begin
		blankt <= 1'b0;
	end else begin
		blankt <= vsyncnow ? ~blankt : blankt;
	end
end

(* async_reg = "true" *) logic [9:0] scanlinepre;
(* async_reg = "true" *) logic [9:0] scanline;
(* async_reg = "true" *) logic [9:0] scanpixelpre;
(* async_reg = "true" *) logic [9:0] scanpixel;
(* async_reg = "true" *) logic blanktogglepre;
(* async_reg = "true" *) logic blanktoggle;

// Vertical blanking and pixel tracking
always_ff @(posedge aclk) begin
	if (~delayedresetn) begin
		scanline <= 10'd0;
		scanlinepre <= 10'd0;
		scanpixelpre <= 10'd0;
		scanpixel <= 10'd0;
		blanktogglepre <= 1'b0;
		blanktoggle <= 1'b0;
	end else begin
		scanlinepre <= video_y;
		scanline <= scanlinepre;
		scanpixelpre <= video_x;
		scanpixel <= scanpixelpre;
		blanktogglepre <= blankt;
		blanktoggle <= blanktogglepre;
	end
end

// {0,scanline[9:0],vsynctoggle[0:0]}
assign vpustate = {21'd0, scanline, blanktoggle};

typedef enum logic [2:0] {DETECTFRAMESTART, STARTLOAD, TRIGGERBURST, DATABURST, ADVANCESCANLINEADDRESS} scanstatetype;
scanstatetype scanstate;

logic [6:0] rdata_cnt;

always_ff @(posedge aclk) begin
	if (~delayedresetn) begin
		scanlinewe <= 1'b0;
		m_axi.arvalid <= 0;
		m_axi.rready <= 0;
		rdata_cnt <= 7'd0;
		scanoffset <= 32'd0;
		scanlinewa <= 7'd0;
		scanstate <= DETECTFRAMESTART;
	end else begin
		scanlinewe <= 1'b0;
		case (scanstate)
			DETECTFRAMESTART: begin
				// When we reach the last odd scanline, start loading the cache
				if (scanenable && (scanline == lastscanline)) begin
					scanoffset <= scanaddr;
					scanstate <= STARTLOAD;
				end else begin
					scanstate <= DETECTFRAMESTART;
				end
			end

			STARTLOAD: begin
				// Only read on odd lines in 320-wide, or every other line in 640-wide mode
				// The trick here: we'll initially hit odd-even-even-odd sequence which means
				// the cache line we loaded on line 523 will only reload on line 1 after it's been displayed twice in 320 mode
				if ((scanpixel == 640) && (scanline[0] || scanwidth)) begin
					// This has to be a 64 byte cache aligned address to match cache burst reads we're running
					// Each scanline is a multiple of 64 bytes, so no need to further align here unless we have an odd output size (320 and 640 work just fine)
					m_axi.arlen <= burstlen;
					m_axi.araddr <= scanoffset;
					m_axi.arvalid <= (scanline == 10'd479) ? 1'b0 : 1'b1;
					// Keep reading as long as we're not on last line
					scanstate <= scanline == 10'd479 ? DETECTFRAMESTART : TRIGGERBURST;
				end else begin
					scanstate <= STARTLOAD;
				end
			end

			TRIGGERBURST: begin
				if (/*m_axi.arvalid && */m_axi.arready) begin
					rdata_cnt <= 0;
					m_axi.arvalid <= 0;
					m_axi.rready <= 1;
					scanstate <= DATABURST;
				end else begin
					scanstate <= TRIGGERBURST;
				end
			end

			DATABURST: begin
				if (m_axi.rvalid  /*&& m_axi.rready*/) begin
					// Load data into scanline cache in 128bit chunks (16 pixels at 8bpp, 20 of them)
					// NOTE: video mode control sets up burst length to either 40 or 80
					scanlinewe <= 1'b1;
					scanlinewa <= rdata_cnt;
					scanlinedin <= m_axi.rdata;
					rdata_cnt <= rdata_cnt + 'd1;
					m_axi.rready <= ~m_axi.rlast;
					scanstate <= m_axi.rlast ? ADVANCESCANLINEADDRESS : DATABURST;
				end else begin
					scanstate <= DATABURST;
				end
			end

			ADVANCESCANLINEADDRESS: begin
				// Wait for and load next scanline
				scanoffset <= scanoffset + scaninc;
				scanstate <= STARTLOAD;
			end

		endcase
	end
end

endmodule
