ecilasun/tinysys/hardware/tinysys.srcs/sources_1/new/arbiterlarge.sv

`timescale 1ns / 1ps
`default_nettype none

module arbiterlarge(
	input wire aclk,
	input wire aresetn,
	axi4if.slave axi_s[6:0],	// To slave in ports of master devices
	axi4if.master axi_m );		// To master in port of slave device

// --------------------------------------------------
// Common
// --------------------------------------------------

// Round-robin arbiter with independent read and write arbitration

// NOTE: Expand the enum and state machine for more devices
typedef enum logic [3:0] {INIT, ARBITRATE0, ARBITRATE1, ARBITRATE2, ARBITRATE3, ARBITRATE4, ARBITRATE5, ARBITRATE6, GRANTED} arbiterstatetype;

// --------------------------------------------------
// Read arbiter
// --------------------------------------------------

arbiterstatetype readstate = INIT;
arbiterstatetype rarbstate = ARBITRATE0;

logic [6:0] rreq;
logic [6:0] rgrant;
logic rreqcomplete = 0;

// A request is considered only when an incoming read or write address is valid
genvar rreqgen;
generate
for (rreqgen=0; rreqgen<7; rreqgen++) begin
	always_comb begin
		rreq[rreqgen] = axi_s[rreqgen].arvalid;
	end
end
endgenerate

// A read grant is complete once we get a notification for read completion
always_comb begin
	rreqcomplete = axi_m.rvalid && axi_m.rlast;
end

// Read grants
genvar rgnt;
generate
for (rgnt=0; rgnt<7; rgnt++) begin
	always_comb begin
		axi_s[rgnt].arready = rgrant[rgnt] ? axi_m.arready : 0;
		axi_s[rgnt].rdata   = rgrant[rgnt] ? axi_m.rdata : 'dz;
		axi_s[rgnt].rresp   = rgrant[rgnt] ? axi_m.rresp : 0;
		axi_s[rgnt].rvalid  = rgrant[rgnt] ? axi_m.rvalid : 0;
		axi_s[rgnt].rlast   = rgrant[rgnt] ? axi_m.rlast : 0;
	end
end
endgenerate

always_comb begin
	unique case(1'b1)
		rgrant[6]: begin
			axi_m.araddr	= axi_s[6].araddr;
			axi_m.arvalid	= axi_s[6].arvalid;
			axi_m.arlen		= axi_s[6].arlen;
			axi_m.arsize	= axi_s[6].arsize;
			axi_m.arburst	= axi_s[6].arburst;
			axi_m.rready	= axi_s[6].rready;
		end
		rgrant[5]: begin
			axi_m.araddr	= axi_s[5].araddr;
			axi_m.arvalid	= axi_s[5].arvalid;
			axi_m.arlen		= axi_s[5].arlen;
			axi_m.arsize	= axi_s[5].arsize;
			axi_m.arburst	= axi_s[5].arburst;
			axi_m.rready	= axi_s[5].rready;
		end
		rgrant[4]: begin
			axi_m.araddr	= axi_s[4].araddr;
			axi_m.arvalid	= axi_s[4].arvalid;
			axi_m.arlen		= axi_s[4].arlen;
			axi_m.arsize	= axi_s[4].arsize;
			axi_m.arburst	= axi_s[4].arburst;
			axi_m.rready	= axi_s[4].rready;
		end
		rgrant[3]: begin
			axi_m.araddr	= axi_s[3].araddr;
			axi_m.arvalid	= axi_s[3].arvalid;
			axi_m.arlen		= axi_s[3].arlen;
			axi_m.arsize	= axi_s[3].arsize;
			axi_m.arburst	= axi_s[3].arburst;
			axi_m.rready	= axi_s[3].rready;
		end
		rgrant[2]: begin
			axi_m.araddr	= axi_s[2].araddr;
			axi_m.arvalid	= axi_s[2].arvalid;
			axi_m.arlen		= axi_s[2].arlen;
			axi_m.arsize	= axi_s[2].arsize;
			axi_m.arburst	= axi_s[2].arburst;
			axi_m.rready	= axi_s[2].rready;
		end
		rgrant[1]: begin
			axi_m.araddr	= axi_s[1].araddr;
			axi_m.arvalid	= axi_s[1].arvalid;
			axi_m.arlen		= axi_s[1].arlen;
			axi_m.arsize	= axi_s[1].arsize;
			axi_m.arburst	= axi_s[1].arburst;
			axi_m.rready	= axi_s[1].rready;
		end
		rgrant[0]: begin
			axi_m.araddr	= axi_s[0].araddr;
			axi_m.arvalid	= axi_s[0].arvalid;
			axi_m.arlen		= axi_s[0].arlen;
			axi_m.arsize	= axi_s[0].arsize;
			axi_m.arburst	= axi_s[0].arburst;
			axi_m.rready	= axi_s[0].rready;
		end
		default: begin
			axi_m.araddr	= 32'dz;
			axi_m.arvalid	= 0;
			axi_m.arlen		= 0;
			axi_m.arsize	= 0;
			axi_m.arburst	= 0;
			axi_m.rready	= 0;
		end
	endcase
end

always_ff @(posedge aclk) begin
	if (~aresetn) begin
		readstate <= INIT;
		rarbstate <= ARBITRATE0;
		rgrant <= 0;
	end else begin
		unique case(readstate)
			INIT: begin
				rgrant <= 0;
				readstate <= ARBITRATE0;
			end
	
			ARBITRATE0: begin
				readstate <= (|rreq) ? GRANTED : ARBITRATE0;
				priority case(1'b1)
					rreq[1]: begin rgrant <= 7'b0000010; rarbstate <= ARBITRATE1; end
					rreq[2]: begin rgrant <= 7'b0000100; rarbstate <= ARBITRATE2; end
					rreq[3]: begin rgrant <= 7'b0001000; rarbstate <= ARBITRATE3; end
					rreq[4]: begin rgrant <= 7'b0010000; rarbstate <= ARBITRATE4; end
					rreq[5]: begin rgrant <= 7'b0100000; rarbstate <= ARBITRATE5; end
					rreq[6]: begin rgrant <= 7'b1000000; rarbstate <= ARBITRATE6; end
					rreq[0]: begin rgrant <= 7'b0000001; rarbstate <= ARBITRATE0; end
					default: rgrant <= 7'b0000000;
				endcase
			end
	
			ARBITRATE1: begin
				readstate <= (|rreq) ? GRANTED : ARBITRATE1;
				priority case(1'b1)
					rreq[2]: begin rgrant <= 7'b0000100; rarbstate <= ARBITRATE2; end
					rreq[3]: begin rgrant <= 7'b0001000; rarbstate <= ARBITRATE3; end
					rreq[4]: begin rgrant <= 7'b0010000; rarbstate <= ARBITRATE4; end
					rreq[5]: begin rgrant <= 7'b0100000; rarbstate <= ARBITRATE5; end
					rreq[6]: begin rgrant <= 7'b1000000; rarbstate <= ARBITRATE6; end
					rreq[0]: begin rgrant <= 7'b0000001; rarbstate <= ARBITRATE0; end
					rreq[1]: begin rgrant <= 7'b0000010; rarbstate <= ARBITRATE1; end
					default: rgrant <= 7'b0000000;
				endcase
			end
	
			ARBITRATE2: begin
				readstate <= (|rreq) ? GRANTED : ARBITRATE2;
				priority case(1'b1)
					rreq[3]: begin rgrant <= 7'b0001000; rarbstate <= ARBITRATE3; end
					rreq[4]: begin rgrant <= 7'b0010000; rarbstate <= ARBITRATE4; end
					rreq[5]: begin rgrant <= 7'b0100000; rarbstate <= ARBITRATE5; end
					rreq[6]: begin rgrant <= 7'b1000000; rarbstate <= ARBITRATE6; end
					rreq[0]: begin rgrant <= 7'b0000001; rarbstate <= ARBITRATE0; end
					rreq[1]: begin rgrant <= 7'b0000010; rarbstate <= ARBITRATE1; end
					rreq[2]: begin rgrant <= 7'b0000100; rarbstate <= ARBITRATE2; end
					default: rgrant <= 7'b0000000;
				endcase
			end
	
			ARBITRATE3: begin
				readstate <= (|rreq) ? GRANTED : ARBITRATE3;
				priority case(1'b1)
					rreq[4]: begin rgrant <= 7'b0010000; rarbstate <= ARBITRATE4; end
					rreq[5]: begin rgrant <= 7'b0100000; rarbstate <= ARBITRATE5; end
					rreq[6]: begin rgrant <= 7'b1000000; rarbstate <= ARBITRATE6; end
					rreq[0]: begin rgrant <= 7'b0000001; rarbstate <= ARBITRATE0; end
					rreq[1]: begin rgrant <= 7'b0000010; rarbstate <= ARBITRATE1; end
					rreq[2]: begin rgrant <= 7'b0000100; rarbstate <= ARBITRATE2; end
					rreq[3]: begin rgrant <= 7'b0001000; rarbstate <= ARBITRATE3; end
					default: rgrant <= 7'b0000000;
				endcase
			end
	
			ARBITRATE4: begin
				readstate <= (|rreq) ? GRANTED : ARBITRATE4;
				priority case(1'b1)
					rreq[5]: begin rgrant <= 7'b0100000; rarbstate <= ARBITRATE5; end
					rreq[6]: begin rgrant <= 7'b1000000; rarbstate <= ARBITRATE6; end
					rreq[0]: begin rgrant <= 7'b0000001; rarbstate <= ARBITRATE0; end
					rreq[1]: begin rgrant <= 7'b0000010; rarbstate <= ARBITRATE1; end
					rreq[2]: begin rgrant <= 7'b0000100; rarbstate <= ARBITRATE2; end
					rreq[3]: begin rgrant <= 7'b0001000; rarbstate <= ARBITRATE3; end
					rreq[4]: begin rgrant <= 7'b0010000; rarbstate <= ARBITRATE4; end
					default: rgrant <= 7'b0000000;
				endcase
			end
	
			ARBITRATE5: begin
				readstate <= (|rreq) ? GRANTED : ARBITRATE5;
				priority case(1'b1)
					rreq[6]: begin rgrant <= 7'b1000000; rarbstate <= ARBITRATE6; end
					rreq[0]: begin rgrant <= 7'b0000001; rarbstate <= ARBITRATE0; end
					rreq[1]: begin rgrant <= 7'b0000010; rarbstate <= ARBITRATE1; end
					rreq[2]: begin rgrant <= 7'b0000100; rarbstate <= ARBITRATE2; end
					rreq[3]: begin rgrant <= 7'b0001000; rarbstate <= ARBITRATE3; end
					rreq[4]: begin rgrant <= 7'b0010000; rarbstate <= ARBITRATE4; end
					rreq[5]: begin rgrant <= 7'b0100000; rarbstate <= ARBITRATE5; end
					default: rgrant <= 7'b0000000;
				endcase
			end
	
			ARBITRATE6: begin
				readstate <= (|rreq) ? GRANTED : ARBITRATE6;
				priority case(1'b1)
					rreq[0]: begin rgrant <= 7'b0000001; rarbstate <= ARBITRATE0; end
					rreq[1]: begin rgrant <= 7'b0000010; rarbstate <= ARBITRATE1; end
					rreq[2]: begin rgrant <= 7'b0000100; rarbstate <= ARBITRATE2; end
					rreq[3]: begin rgrant <= 7'b0001000; rarbstate <= ARBITRATE3; end
					rreq[4]: begin rgrant <= 7'b0010000; rarbstate <= ARBITRATE4; end
					rreq[5]: begin rgrant <= 7'b0100000; rarbstate <= ARBITRATE5; end
					rreq[6]: begin rgrant <= 7'b1000000; rarbstate <= ARBITRATE6; end
					default: rgrant <= 7'b0000000;
				endcase
			end
	
			GRANTED: begin
				readstate <= rreqcomplete ? rarbstate : GRANTED;
			end
		endcase
	end
end

// --------------------------------------------------
// Write arbiter
// --------------------------------------------------

arbiterstatetype writestate = INIT;
arbiterstatetype warbstate = ARBITRATE0;

logic [6:0] wreq;
logic [6:0] wgrant;
logic wreqcomplete = 0;

// A request is considered only when an incoming read or write address is valid
genvar wreqgen;
generate
for (wreqgen=0; wreqgen<7; wreqgen++) begin
	always_comb begin
		wreq[wreqgen] = axi_s[wreqgen].awvalid;
	end
end
endgenerate

// A write grant is complete once we get a notification for write completion
always_comb begin
	wreqcomplete = axi_m.bvalid;
end

genvar wgnt;
generate
for (wgnt=0; wgnt<7; wgnt++) begin
	always_comb begin
		axi_s[wgnt].awready = wgrant[wgnt] ? axi_m.awready : 0;
		axi_s[wgnt].wready  = wgrant[wgnt] ? axi_m.wready : 0;
		axi_s[wgnt].bresp   = wgrant[wgnt] ? axi_m.bresp : 0;
		axi_s[wgnt].bvalid  = wgrant[wgnt] ? axi_m.bvalid : 0;
	end
end
endgenerate

always_comb begin
	unique case(1'b1)
		wgrant[6]: begin
			axi_m.awaddr	= axi_s[6].awaddr;
			axi_m.awvalid	= axi_s[6].awvalid;
			axi_m.awlen		= axi_s[6].awlen;
			axi_m.awsize	= axi_s[6].awsize;
			axi_m.awburst	= axi_s[6].awburst;
			axi_m.wdata		= axi_s[6].wdata;
			axi_m.wstrb		= axi_s[6].wstrb;
			axi_m.wvalid	= axi_s[6].wvalid;
			axi_m.wlast		= axi_s[6].wlast;
			axi_m.bready	= axi_s[6].bready;
		end
		wgrant[5]: begin
			axi_m.awaddr	= axi_s[5].awaddr;
			axi_m.awvalid	= axi_s[5].awvalid;
			axi_m.awlen		= axi_s[5].awlen;
			axi_m.awsize	= axi_s[5].awsize;
			axi_m.awburst	= axi_s[5].awburst;
			axi_m.wdata		= axi_s[5].wdata;
			axi_m.wstrb		= axi_s[5].wstrb;
			axi_m.wvalid	= axi_s[5].wvalid;
			axi_m.wlast		= axi_s[5].wlast;
			axi_m.bready	= axi_s[5].bready;
		end
		wgrant[4]: begin
			axi_m.awaddr	= axi_s[4].awaddr;
			axi_m.awvalid	= axi_s[4].awvalid;
			axi_m.awlen		= axi_s[4].awlen;
			axi_m.awsize	= axi_s[4].awsize;
			axi_m.awburst	= axi_s[4].awburst;
			axi_m.wdata		= axi_s[4].wdata;
			axi_m.wstrb		= axi_s[4].wstrb;
			axi_m.wvalid	= axi_s[4].wvalid;
			axi_m.wlast		= axi_s[4].wlast;
			axi_m.bready	= axi_s[4].bready;
		end
		wgrant[3]: begin
			axi_m.awaddr	= axi_s[3].awaddr;
			axi_m.awvalid	= axi_s[3].awvalid;
			axi_m.awlen		= axi_s[3].awlen;
			axi_m.awsize	= axi_s[3].awsize;
			axi_m.awburst	= axi_s[3].awburst;
			axi_m.wdata		= axi_s[3].wdata;
			axi_m.wstrb		= axi_s[3].wstrb;
			axi_m.wvalid	= axi_s[3].wvalid;
			axi_m.wlast		= axi_s[3].wlast;
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
					wreq[6]: begin wgrant <= 7'b1000000; warbstate <= ARBITRATE6; end
					default: wgrant <= 7'b0000000;
				endcase
			end
	
			GRANTED: begin
				writestate <= wreqcomplete ? warbstate : GRANTED;
			end
		endcase
	end
end

endmodule
