ecilasun/tinysys/software/ROMs/OS/tinyos/gdbstub.c

#include "basesystem.h"
#include "uart.h"
#include "serialinput.h"
#include "rombase.h"
#include "serialinringbuffer.h"
#include "task.h"
#include "keyringbuffer.h"
#include "mini-printf.h"
#include "mini-scanf.h"
#include "gdbstub.h"
#include <stdlib.h>
#include <string.h>

static char *packetData = (char *)GDB_PACKET_BUFFER;
static char *responseData = (char *)GDB_RESPONSE_BUFFER;
static struct GDBContext *s_gdbcontext = NULL;

// Initialize GDB stub
void GDBStubInit()
{
	s_gdbcontext = (struct GDBContext *)GDB_DEBUG_DATA;

	for (int i=0; i<MAX_HARTS*TASK_MAX*MAX_BREAKPOINTS; ++i)
	{
		s_gdbcontext->breakpoints[i] = 0;
		s_gdbcontext->replacedInstructions[i] = 0;
		s_gdbcontext->prevpointStatus[i] = 0;
		s_gdbcontext->breakpointStatus[i] = 0;
		s_gdbcontext->breakpointSignalled[i] = 0;
	}

	s_gdbcontext->debuggerAttached = 0;
	s_gdbcontext->packetCursor = 0;
	s_gdbcontext->haveResponse = 0;
	s_gdbcontext->isackresponse = 0;
	s_gdbcontext->currentGCPU = 0;
	s_gdbcontext->currentGProcess = 2;
	s_gdbcontext->currentCCPU = 0;
	s_gdbcontext->currentCProcess = 2;
	s_gdbcontext->currentCPU = 0;		// First CPU
	s_gdbcontext->currentThread = 2;	// User process
}

uint32_t GDBHexToUint(char *hex)
{
	uint32_t val = 0;
	while (*hex) {
		uint8_t nibble = *hex++;
		if (nibble >= '0' && nibble <= '9')
			nibble = nibble - '0';
		else if (nibble >= 'a' && nibble <='f')
			nibble = nibble - 'a' + 10;
		else if (nibble >= 'A' && nibble <='F')
			nibble = nibble - 'A' + 10;
		val = (val << 4) | (nibble & 0xF);
	}
	return val;
}

uint32_t GDBDecToUint(char *dec)
{
	uint32_t val = 0;
	while (*dec) {
		uint8_t digit = *dec++;
		if (digit >= '0' && digit <= '9')
			digit = digit - '0';
		val = (val*10) + digit;
	}
	return val;
}

uint8_t GDBChecksum(const char *data)
{
	uint8_t sum = 0;
	while (*data)
	{
		sum += (uint8_t)*data++;
	}
	return sum;
}

uint32_t GDBIsDebugging()
{
	return s_gdbcontext->debuggerAttached;
}

void GDBSignalBreakpoint(const uint32_t _hartID, const uint32_t _taskID, const uint32_t _pc, uint32_t _sigtype)
{
	uint32_t offset = _hartID*TASK_MAX*MAX_BREAKPOINTS+_taskID*MAX_BREAKPOINTS;
	if (s_gdbcontext->breakpointSignalled[offset+0] != 1)
	{
		if (_sigtype == GDB_SIGNAL_ILL)
			strcpy(responseData, "S04"); // Illegal instruction
		else if (_sigtype == GDB_SIGNAL_TRAP)
			strcpy(responseData, "S05"); // Breakpoint
		else
			strcpy(responseData, "S19"); // Generic Stop
		mini_snprintf(responseData + strlen(responseData), 1023 - strlen(responseData), "thread:%x;", _taskID);
		uint8_t checksum = GDBChecksum(responseData);
		UARTPrintf("+$%s#%02X", responseData, checksum);
		s_gdbcontext->breakpointSignalled[offset+0] = 1; // Now, what does GDB do so that we can reset signalled state?
	}
}

void GDBAddBreakpoint(uint32_t _hartID, uint32_t _taskID, uint32_t _address)
{
	uint32_t offset = _hartID*TASK_MAX*MAX_BREAKPOINTS+_taskID*MAX_BREAKPOINTS;
	// Find an empty slot
	for (int i=0; i<MAX_BREAKPOINTS; ++i)
	{
		// Find an empty slot
		if (s_gdbcontext->breakpoints[offset+i] == 0)
		{
			// Enable the breakpoint
			s_gdbcontext->breakpoints[offset+i] = _address;
			s_gdbcontext->breakpointStatus[offset+i] = 1;
			break;
		}
	}
}

void GDBRemoveBreakpoint(uint32_t _hartID, uint32_t _taskID, uint32_t _address)
{
	uint32_t offset = _hartID*TASK_MAX*MAX_BREAKPOINTS+_taskID*MAX_BREAKPOINTS;
	for (int i=0; i<MAX_BREAKPOINTS; ++i)
	{
		// Found the breakpoint?
		if (s_gdbcontext->breakpoints[offset+i] == _address)
		{
			// Disable the breakpoint and empty the slot
			s_gdbcontext->breakpoints[offset+i] = 0;
			s_gdbcontext->breakpointStatus[offset+i] = 0;
			break;
		}
	}
}

void GDBUpdateBreakpoints(const uint32_t _hartID, const uint32_t _taskID)
{
	// Check if any breakpoint status has changed and swap instructions as needed
	uint32_t offset = _hartID*TASK_MAX*MAX_BREAKPOINTS+_taskID*MAX_BREAKPOINTS;
	for (int k=0; k<MAX_BREAKPOINTS; ++k)
	{
		if (s_gdbcontext->breakpoints[offset+k] != 0)
		{
			// Check if the breakpoint status has changed
			if (s_gdbcontext->prevpointStatus[offset+k] != s_gdbcontext->breakpointStatus[offset+k])
			{
				// Swap instructions
				if (s_gdbcontext->breakpointStatus[offset+k] == 1)
				{
					// Get the instruction at the breakpoint address
					uint32_t instruction = *((uint32_t *)s_gdbcontext->breakpoints[offset+k]);
					// Enable breakpoint
					s_gdbcontext->replacedInstructions[offset+k] = instruction;
					_task_replace_instruction(0x00100073, s_gdbcontext->breakpoints[offset+k]);
				}
				else
				{
					// Disable breakpoint
					_task_replace_instruction(s_gdbcontext->replacedInstructions[offset+k], s_gdbcontext->breakpoints[offset+k]);
				}

				// Update previous status
				s_gdbcontext->prevpointStatus[offset+k] = s_gdbcontext->breakpointStatus[offset+k];
			}
		}
	}
}

void GDBQSupported()
{
	packetData += 10; // Skip 'qSupported'

	// We have multiple queries in the packet, separated by ';'
	// First query starts with ':', so skip that
	if (packetData[0] == ':')
		packetData++;
	
	strcat(responseData, "PacketSize=1024;qXfer:threads:read+;");

	// Parse queries
	char *command = strtok(packetData, ";");
	while (command != NULL)
	{
		if (strstr(command, "swbreak") == command)
		{
			// Can only do sofware breakpoints (i.e. replace instructions with ebreak and save them in a table)
			strcat(responseData, "swbreak+;");
		}
		else if (strstr(command, "hwbreak") == command)
		{
			// Can't do hardware breakpoints
			strcat(responseData, "hwbreak-;");
		}
		else if (strstr(command, "vContSupported") == command)
		{
			// vCont supported
			strcat(responseData, "vContSupported+;");
		}
		else if (strstr(command, "multiprocess") == command)
		{
			// Only one user process with multiple threads at one time
			strcat(responseData, "multiprocess-;");
		}
		else
		{
			// Ignore unknown queries
			//kprintf("? %s\n", command);
			//strcat(responseData, "-");
		}
		command = strtok(NULL, ";");
	}

	s_gdbcontext->haveResponse = 1;
}

void GDBThreadOp()
{
	// Set thread for subsequent operations

	packetData++; // Skip 'H'

	if (packetData[0] == 'g') // Hg
	{
		packetData++; // Skip 'g'

		// Parse process/thread ID
		int tid;
		c_sscanf(packetData, "p%x", &tid);
		tid = tid <= 0 ? 0 : tid - 1;

		kprintf("g %d\n", tid);
		s_gdbcontext->currentGCPU = 0; // TODO: Find out from thread ID
		s_gdbcontext->currentGProcess = tid;

		strcpy(responseData, "OK");
		s_gdbcontext->haveResponse = 1;
	}
	else if (packetData[0] == 'c') // Hc
	{
		packetData++; // Skip 'c'

		int tid;
		c_sscanf(packetData, "p%x", &tid);
		tid = tid <= 0 ? 0 : tid - 1;

		kprintf("c %d\n", tid);
		s_gdbcontext->currentCCPU = 0; // TODO: Find out from thread ID
		s_gdbcontext->currentCProcess = tid;

		strcpy(responseData, "OK");
		s_gdbcontext->haveResponse = 1;
	}
}

void GDBQTStatus()
{
	// Empty response
	strcpy(responseData, "");
	s_gdbcontext->haveResponse = 1;
}

void GDBThreadsRead()
{
	packetData += 19; // Skip 'qXfer:threads:read:'
	packetData++; // Skip second ':'

	int offset, length;
	c_sscanf(packetData, "%d,%d", &offset, &length);

	// m: more data, l: last packet
	strcpy(responseData, "l<?xml version=\"1.0\"?>\n<threads>\n");

	// NOTE: The OS thread (CPU#0 thread#0) can't be debugged as it's running the OS and the debugger
	for (int cpu=0; cpu<MAX_HARTS; ++cpu)
	{
		struct STaskContext *ctx = _task_get_context(cpu);

		// Skip the OS threads
		for (int j=cpu==0 ? 2 : 1; j<ctx->numTasks; ++j)
		{
			struct STask *task = &ctx->tasks[j];
			// Apparently GDB expects thread IDs across CPUs to be unique
			mini_snprintf(responseData, 1023, "%s\t<thread id=\"%d\" core=\"%d\" name=\"%s\" handle=\"%x\">%s [CPU%d]</thread>\n", responseData, j+1, cpu, task->name, cpu*TASK_MAX+j, task->name, cpu);
		}
	}

	strcat(responseData, "</threads>\n");

	s_gdbcontext->haveResponse = 1;
}

void GDBThreadInfo()
{
	// GDB expects the first thread in the response to be able to stop.
	// We'll have to deny that for the OS threads.
	strcpy(responseData, "m ");
	for (int cpu=0; cpu<MAX_HARTS; ++cpu)
	{
		struct STaskContext *ctx = _task_get_context(cpu);

		// Skip the OS threads
		for (int j=cpu==0 ? 2 : 1; j<ctx->numTasks; ++j)
		{
			//struct STask *task = &ctx->tasks[i];
			mini_snprintf(responseData, 1023, "%s%d", responseData, j+1);
			strcat(responseData, ",");
		}
	}

	// Delete the last ','
	responseData[strlen(responseData)-1] = 0;

	s_gdbcontext->haveResponse = 1;
}

void GDBQAttached()
{
	packetData += 9; // Skip 'qAttached'
	packetData++; // Skip ':'

	uint32_t processid;
	c_sscanf(packetData, "%x", &processid);
	
	//kprintf("?attached(%d)\n", processid);

	// 1: Attached to existing process, 0: Created new process
	strcpy(responseData, "1");
	s_gdbcontext->haveResponse = 1;
}

void GDBMemRead()
{
	packetData++; // Skip 'm'

	// Parse address
	uint32_t addrs, numbytes;
	c_sscanf(packetData, "%x,%d", &addrs, &numbytes);

	// Read memory and format response
	for (uint32_t i = 0; i < numbytes; ++i)
	{
		uint8_t byte = *((uint8_t *)(addrs + i));
		mini_snprintf(responseData, 1023, "%s%02x", responseData, byte);
	}

	s_gdbcontext->haveResponse = 1;
}

void GDBMemWrite()
{
	packetData++; // Skip 'M'

	// Parse address
	uint32_t addrs, numbytes;
	int skip = c_sscanf(packetData, "%x,%d:", &addrs, &numbytes);
	packetData += skip;

	// Write memory
	for (uint32_t i = 0; i < numbytes; ++i)
	{
		uint8_t byte = GDBHexToUint(packetData);
		*((uint8_t *)(addrs + i)) = byte;
		packetData += 2;
	}

	strcpy(responseData, "OK");
	s_gdbcontext->haveResponse = 1;
}

void GDBReadRegisters()
{
	// Registers for 'currentGProcess'

	struct STaskContext *ctx = _task_get_context(0); // CPU0
	struct STask *task = &ctx->tasks[s_gdbcontext->currentGProcess];

	// Since we're stashing PC here, we'll just return 0 for zero register instead
	mini_snprintf(responseData, 1023, "%s00000000", responseData);

	// General purpose registers - float registers are aliased to these in our arhitecture
	for (int i=1; i<32; ++i)
	{
		uint32_t reg = task->regs[i];
		mini_snprintf(responseData + strlen(responseData), 1023 - strlen(responseData), "%02x%02x%02x%02x",
					(reg >> 0) & 0xFF,
					(reg >> 8) & 0xFF,
					(reg >> 16) & 0xFF,
					(reg >> 24) & 0xFF);
	}

	// PC comes last
	uint32_t pc = task->regs[0];
	mini_snprintf(responseData + strlen(responseData), 1023 - strlen(responseData), "%02x%02x%02x%02x",
				(pc >> 0) & 0xFF,
				(pc >> 8) & 0xFF,
				(pc >> 16) & 0xFF,
				(pc >> 24) & 0xFF);

	s_gdbcontext->haveResponse = 1;
}

void GDBWriteRegisters()
{
	packetData++; // Skip 'G'

	// Parse registers
	struct STaskContext *ctx = _task_get_context(0); // CPU0
	struct STask *task = &ctx->tasks[s_gdbcontext->currentGProcess];

	for (int i=1; i<32; ++i)
	{
		uint32_t reg = GDBHexToUint(packetData);
		task->regs[i] = reg;
		packetData += 8;
	}

	// PC comes last
	uint32_t pc = GDBHexToUint(packetData);
	task->regs[0] = pc;

	strcpy(responseData, "OK");
	s_gdbcontext->haveResponse = 1;
}

void GDBVCont()
{
	packetData += 6; // Skip 'vCont'

	// Parse commands
	char *command = strtok(packetData, ";");
	while (command != NULL)
	{
		if (strstr(command, "?") == command)
		{
			strcpy(responseData, "vCont;c;C;s;S;");
			s_gdbcontext->haveResponse = 1;
		}
		else if (strstr(command, "c") == command)
		{
			// Continue
			strcpy(responseData, "S05");
			s_gdbcontext->haveResponse = 1;
		}
		else if (strstr(command, "s") == command)
		{
			// Step
			strcpy(responseData, "S05");
			s_gdbcontext->haveResponse = 1;
		}
		else
		{
			kprintf("Unknown vCont: %s\n", command);
		}
		command = strtok(NULL, ";");
	}
}

void GDBSetThread()
{
	packetData++; // Skip 'T'

	// Parse thread ID
	char *threadStr = strtok(packetData, ";");
	if (threadStr != NULL)
	{
		int tid;
		c_sscanf(threadStr, "p%x", &tid);
		tid = tid <= 0 ? 0 : tid - 1;

		kprintf("T %d\n", tid);
		s_gdbcontext->currentCPU = 0; // TODO: Find out from thread ID
		s_gdbcontext->currentThread = tid;

		strcpy(responseData, "OK");
		s_gdbcontext->haveResponse = 1;
	}
}

void GDBBreak()
{
	if (s_gdbcontext->debuggerAttached == 0)
	{
		// Pass this through to the CLI for now
		// Later on we'll let the GDB stub handle this
		uint8_t drain = 0x03;
		KeyRingBufferWrite(&drain, 1);
	}
	else
	{
		// Add a software breakpoint at the current PC to stop the process
		GDBAddBreakpoint(s_gdbcontext->currentGCPU, s_gdbcontext->currentGProcess, _task_get_context(s_gdbcontext->currentGCPU)->tasks[s_gdbcontext->currentGProcess].regs[0]);

		// Stopped due to CTRL+C
		strcpy(responseData, "T02");
		s_gdbcontext->haveResponse = 1;
	}
}

void GDBParseCommands()
{
	if (packetData[0] == 0x03) // CTRL+C
	{
		GDBBreak();
	}
	else if (strstr(packetData, "m") == packetData)
	{
		GDBMemRead();
	}
	else if (strstr(packetData, "M") == packetData)
	{
		GDBMemWrite();
	}
	else if (strstr(packetData, "g") == packetData)
	{
		GDBReadRegisters();
	}
	else if (strstr(packetData, "G") == packetData)
	{
		GDBWriteRegisters();
	}
	else if (strstr(packetData, "H") == packetData)
	{
		GDBThreadOp();
	}
	else if (strstr(packetData, "T") == packetData)
	{
		GDBSetThread();
	}
	else if (strstr(packetData, "c") == packetData)
	{
		// Continue

		strcpy(responseData, "OK"); // or S05 or other codes if process stops
		s_gdbcontext->haveResponse = 1;
	}
	else if (strstr(packetData, "D") == packetData)
	{
		s_gdbcontext->debuggerAttached = 0;

		// TODO: Detach (i.e. resume process and restore all breakpoints)

		strcpy(responseData, "OK");
		s_gdbcontext->haveResponse = 1;
	}
	else if (strstr(packetData, "qC") == packetData)
	{
		mini_snprintf(responseData, 1023, "QC %d", s_gdbcontext->currentThread);
		s_gdbcontext->haveResponse = 1;
	}
	else if (strstr(packetData, "Z0") == packetData)
	{
		// TODO: Insert breakpoint
		strcpy(responseData, "OK");
		s_gdbcontext->haveResponse = 1;
	}
	else if (strstr(packetData, "z0") == packetData)
	{
		// TODO: Remove breakpoint
		strcpy(responseData, "OK");
		s_gdbcontext->haveResponse = 1;
	}
	else if (strstr(packetData, "qSupported") == packetData)
	{
		s_gdbcontext->debuggerAttached = 1;
		GDBQSupported();
	}
	else if (strstr(packetData, "vKill") == packetData)
	{
		s_gdbcontext->debuggerAttached = 0;

		// Kill user process and its threads
		struct STaskContext *ctx0 = _task_get_context(0);
		for (int i=2; i<ctx0->numTasks; ++i)
			_task_exit_task_with_id(ctx0, i, 0);
		struct STaskContext *ctx1 = _task_get_context(1);
		for (int i=1; i<ctx0->numTasks; ++i)
			_task_exit_task_with_id(ctx1, i, 0);

		strcpy(responseData, "OK");
		s_gdbcontext->haveResponse = 1;
	}
	else if (strstr(packetData, "qXfer:threads:read") == packetData)
	{
		GDBThreadsRead();
	}
	else if (strstr(packetData, "qTStatus") == packetData)
	{
		GDBQTStatus();
	}
	else if (strstr(packetData, "qfThreadInfo") == packetData)
	{
		GDBThreadInfo();
	}
	else if (strstr(packetData, "qAttached") == packetData)
	{
		GDBQAttached();
	}
	else if (strstr(packetData, "qSymbol") == packetData)
	{
		// Empty response
		s_gdbcontext->haveResponse = 1;
	}
	else if (strstr(packetData, "qsThreadInfo") == packetData)
	{
		// No more threads
		strcpy(responseData, "l");
		s_gdbcontext->haveResponse = 1;
	}
	else if (strstr(packetData, "vMustReplyEmpty"))
	{
		// Empty response
		s_gdbcontext->haveResponse = 1;
	}
	else if (strstr(packetData, "qOffsets") == packetData)
	{
		// Empty response
		s_gdbcontext->haveResponse = 1;
	}
	else if (strstr(packetData, "?") == packetData)
	{
		// S00 if the process is not halted
		strcpy(responseData, "S00");
		s_gdbcontext->haveResponse = 1;
	}
	else if (strstr(packetData, "vCont") == packetData)
	{
		GDBVCont();
		s_gdbcontext->haveResponse = 1;
	}
	else
	{
		//kprintf("unknown command: %s\n", packetData);
		strcpy(responseData, "-");
		s_gdbcontext->isackresponse = 1;
		s_gdbcontext->haveResponse = 1;
	}

	if (s_gdbcontext->haveResponse)
	{
		if (s_gdbcontext->isackresponse)
		{
			UARTPrintf("%s", responseData);
			//kprintf("(N)ACK: %s\n", responseData);
		}
		else
		{
			uint8_t checksum = GDBChecksum(responseData);
			UARTPrintf("+$%s#%02X", responseData, checksum);
			//kprintf("Response: +$%s#%02X\n", responseData, checksum);
		}
	}
}

void GDBStubBeginPacket()
{
	responseData[0] = 0;
	s_gdbcontext->packetCursor = 0;
	s_gdbcontext->haveResponse = 0;
	s_gdbcontext->isackresponse = 0;
}

void GDBStubEndPacket()
{
	// Null-terminate the packet
	packetData[s_gdbcontext->packetCursor++] = 0;

	// TODO: Parse and respond to packet contents
	GDBParseCommands();
}

void GDBStubAddByte(uint8_t byte)
{
	packetData[s_gdbcontext->packetCursor++] = byte;
}
