ecilasun/tinysys/hardware/tinysys.srcs/sources_1/new/decoder.sv

`timescale 1ns / 1ps
`default_nettype none

`include "shared.vh"

module decoder(
	input wire [31:0] instruction,		// Raw input instruction
	output bit [15:0] instrOneHotOut,	// Current instruction class
	output bit [3:0] aluop,				// Current ALU op
	output bit [2:0] bluop,				// Current BLU op
	output bit [2:0] func3,				// Sub-instruction
	output bit [6:0] func7,				// Sub-instruction
	output bit [11:0] func12,			// Sub-instruction
	output bit [4:0] rs1,				// Source register one
	output bit [4:0] rs2,				// Source register two
	output bit [4:0] rs3,				// Used by fused multiplyadd/sub
	output bit [4:0] rd,				// Destination register
	output bit [11:0] csroffset,		// Index of selected CSR register
	output bit [31:0] immed,			// Unpacked immediate integer value
	output bit selectimmedasrval2		// Select rval2 or unpacked integer during EXEC
);

wire [15:0] instrOneHot = {
	instruction[6:0]==`OPCODE_OP ? 1'b1:1'b0,
	instruction[6:0]==`OPCODE_OP_IMM ? 1'b1:1'b0,
	instruction[6:0]==`OPCODE_AUIPC ? 1'b1:1'b0,
	instruction[6:0]==`OPCODE_LUI ? 1'b1:1'b0,
	instruction[6:0]==`OPCODE_STORE ? 1'b1:1'b0,
	instruction[6:0]==`OPCODE_LOAD ? 1'b1:1'b0,
	instruction[6:0]==`OPCODE_JAL ? 1'b1:1'b0,
	instruction[6:0]==`OPCODE_JALR ? 1'b1:1'b0,
	instruction[6:0]==`OPCODE_BRANCH ? 1'b1:1'b0,
	instruction[6:0]==`OPCODE_FENCE ? 1'b1:1'b0,
	instruction[6:0]==`OPCODE_SYSTEM ? 1'b1:1'b0,
	instruction[6:0]==`OPCODE_FLOAT_OP ? 1'b1:1'b0,
	// instruction[6:0]==`OPCODE_FLOAT_LDW ? 1'b1:1'b0,
	// instruction[6:0]==`OPCODE_FLOAT_STW ? 1'b1:1'b0,
	instruction[6:0]==`OPCODE_FLOAT_MADD ? 1'b1:1'b0,
	instruction[6:0]==`OPCODE_FLOAT_MSUB ? 1'b1:1'b0,
	instruction[6:0]==`OPCODE_FLOAT_NMSUB ? 1'b1:1'b0,
	instruction[6:0]==`OPCODE_FLOAT_NMADD ? 1'b1:1'b0 };

always_comb begin
	csroffset = {instruction[31:25], instruction[24:20]};
end

// Immed vs rval2 selector
wire selector = instrOneHot[`O_H_JALR] || instrOneHot[`O_H_OP_IMM] || instrOneHot[`O_H_LOAD] || instrOneHot[`O_H_STORE];

// NOTE: Load _is_ recording form but it's delayed vs where we normaly flag 'recording', so it's omitted from list and handled mamually
//wire recordingform = ~(instrOneHot[`O_H_BRANCH] || instrOneHot[`O_H_LOAD] || instrOneHot[`O_H_STORE] || isfpuopcode) || (instrOneHot[`O_H_SYSTEM] & (|func3));

// Instruction encodings
//          31  30  29  28  27  26  25  24  23  22  21  20  19  18  17  16  15  14  13  12  11  10  09  08  07  06  05  04  03  02  01  00  
// R-type:  |funct7                     |rs2                |rs1                |funct3     |rd                 |opcode
// I-type:  |i11:0                                          |rs1                |funct3     |rd                 |opcode
// S-type:  |i11:15                     |rs2                |rs1                |funct3     |i4:0               |opcode
// B-type:  |i12 |i10:5                 |rs2                |rs1                |funct3     |i4:1           |i11|opcode
// U-type:  |i31:12                                                                         |rd                 |opcode
// J-type:  |i20 |i10:1                                 |i11|i19:12                         |rd                 |opcode
// NOTE: 12 bit branch offset is in multiples of 2 in B-type

// Source/destination register indices
wire [4:0] src1 = instruction[19:15];
wire [4:0] src2 = instruction[24:20];
wire [4:0] src3 = instruction[31:27];
wire [4:0] dest = instruction[11:7];

// Sub-functions
wire [2:0] f3 = instruction[14:12];
wire [6:0] f7 = instruction[31:25];
wire [11:0] f12 = instruction[31:20];
wire mathopsel = instruction[30];
wire muldiv = instruction[25];

// Shift in decoded values
always_comb begin
	rs1 = src1;
	rs2 = src2;
	rs3 = src3;
	rd = dest;
	func3 = f3;
	func7 = f7;
	func12 = f12;
	instrOneHotOut = instrOneHot;
	selectimmedasrval2 = selector;	// Use rval2 or immed
end

// Work out ALU op
always_comb begin
	unique case(1'b1)
		instrOneHot[`O_H_OP]: begin
			unique case({muldiv, f3})
				4'b0_000: aluop = mathopsel ? `ALU_SUB : `ALU_ADD;
				4'b0_001: aluop = `ALU_SLL;
				4'b0_011: aluop = `ALU_SLTU;
				4'b0_010: aluop = `ALU_SLT;
				4'b0_110: aluop = `ALU_OR;
				4'b0_111: aluop = `ALU_AND;
				4'b0_101: aluop = mathopsel ? `ALU_SRA : `ALU_SRL;
				4'b0_100: aluop = `ALU_XOR;
				4'b1_000,
				4'b1_001,
				4'b1_010,
				4'b1_011: aluop = `ALU_MUL;
				4'b1_100,
				4'b1_101: aluop = `ALU_DIV;
				4'b1_110,
				4'b1_111: aluop = `ALU_REM;
				default:  aluop = `ALU_NONE;
			endcase
		end

		instrOneHot[`O_H_OP_IMM]: begin
			unique case(f3)
				3'b000: aluop = `ALU_ADD;
				3'b001: aluop = `ALU_SLL;
				3'b011: aluop = `ALU_SLTU;
				3'b010: aluop = `ALU_SLT;
				3'b110: aluop = `ALU_OR;
				3'b111: aluop = `ALU_AND;
				3'b101: aluop = mathopsel ? `ALU_SRA : `ALU_SRL;
				3'b100: aluop = `ALU_XOR;
				default: aluop = `ALU_NONE;
			endcase
		end

		default: begin
			aluop = `ALU_NONE;
		end
	endcase
end

// Work out BLU op
always_comb begin
	unique case(1'b1)
		instrOneHot[`O_H_BRANCH]: begin
			unique case(f3)
				3'b000: bluop = `BLU_EQ;
				3'b001: bluop = `BLU_NE;
				3'b011: bluop = `BLU_NONE;
				3'b010: bluop = `BLU_NONE;
				3'b110: bluop = `BLU_LU;
				3'b111: bluop = `BLU_GEU;
				3'b101: bluop = `BLU_GE;
				3'b100: bluop = `BLU_L;
			endcase
		end

		default: begin
			bluop = `BLU_NONE;
		end
	endcase
end

// Immediate encodings (o stands for instruction word)
//        31  30  29  28  27  26  25  24  23  22  21  20  19  18  17  16  15  14  13  12  11  10  09  08  07  06  05  04  03  02  01  00  
// I-imm: |o31                                                                                |o30:25                 |o24:21         |o20
// S-imm: |o31                                                                                |o30:25                 |o11:8          |o7
// B-imm: |o31                                                                            |o7 |o30:25                 |o11:8          |0
// U-imm: |o31|o30:20                                     |o19:12                         |0
// J-imm: |o31                                            |o19:12                         |o20|o30:25                 |o24:21         |0
// NOTE: All immediate sign bits are at bit 31 for easy sign extension

always_comb begin
	unique case(1'b1)
		// U-imm
		instrOneHot[`O_H_LUI], instrOneHot[`O_H_AUIPC]: begin
			immed = {instruction[31:12], 12'd0};
		end
		// S-imm
		instrOneHot[`O_H_STORE]: begin
			immed = {{21{instruction[31]}}, instruction[30:25], instruction[11:7]};
		end
		// J-imm
		instrOneHot[`O_H_JAL]: begin
			immed = {{12{instruction[31]}}, instruction[19:12], instruction[20], instruction[30:21], 1'b0};
		end
		// B-imm
		instrOneHot[`O_H_BRANCH]: begin
			immed = {{20{instruction[31]}}, instruction[7], instruction[30:25], instruction[11:8], 1'b0};
		end
		// zero extented 5 bit imm encoding for CSR*I instructions
		instrOneHot[`O_H_SYSTEM], instrOneHot[`O_H_FENCE]: begin
			immed = {27'd0, instruction[19:15]};
		end
		// I-imm
		default/*instrOneHot[`O_H_OP_IMM], instrOneHot[`O_H_LOAD], instrOneHot[`O_H_JALR]*/: begin
			immed = {{21{instruction[31]}}, instruction[30:20]};
		end
	endcase
end

endmodule
