ecilasun/tinysys/hardware/tinysys.srcs/sources_1/new/idiv.sv

`timescale 1ns / 1ps
`default_nettype none

// --------------------------------------------------
// Unsigned divider
// --------------------------------------------------

module integerdividerunsigned(
    input wire aclk,
    input wire aresetn,
    input wire start,
    input wire [31:00] dividend,
    input wire [31:00] divisor,
    output logic [31:00] quotient,
    output logic [31:00] remainder,
    output wire ready);

logic [5:0] count;
logic [31:0] reg_q;
logic [31:0] reg_r;
logic [31:0] reg_b;
logic rdy;
logic r_sign;
assign ready = rdy;

typedef enum logic [1:0] {WCMD, DIVLOOP, DIVEND} divcmdmodetype;
divcmdmodetype cmdmode = WCMD;

wire [32:0] sub_addn = ({reg_r,reg_q[31]}+{1'b0,reg_b});
wire [32:0] sub_addm = ({reg_r,reg_q[31]}-{1'b0,reg_b});
wire [31:0] rem = r_sign ? reg_r + reg_b : reg_r;
wire [31:0] quo = reg_q;

always @(posedge aclk) begin
    if (~aresetn) begin
    	rdy <= 1'b0;
    	count <= 6'd0;
		reg_r <= 32'b0;
        cmdmode <= WCMD;
    end else begin
		count <= count+1;
		rdy <= 1'b0;
		unique case (cmdmode)
			WCMD: begin
				r_sign <= 0;
				reg_q <= dividend;
				reg_b <= divisor;
				count <= 0;
				cmdmode <= start ? DIVLOOP : WCMD;
			end
			DIVLOOP: begin
				unique case (r_sign)
					1'b1: begin
						reg_r <= sub_addn[31:0];
						r_sign <= sub_addn[32];
						reg_q <= {reg_q[30:0], ~sub_addn[32]};
					end
					1'b0: begin
						reg_r <= sub_addm[31:0];
						r_sign <= sub_addm[32];
						reg_q <= {reg_q[30:0], ~sub_addm[32]};
					end
				endcase
				rdy <= count[5];
				cmdmode <= count[5] ? DIVEND : DIVLOOP;
				if (count[5]) begin
					remainder <= rem;
					quotient <= quo;
				end else begin
					remainder <= 32'd0;
					quotient <= 32'd0;
				end
			end
			DIVEND: begin
				reg_r <= 32'b0;
				cmdmode <= WCMD;
			end
		endcase
	end
end

endmodule
